baldengineer/Mega-IIe/kicad files/gd rp2040 keyboard proto pcb/kicad/README.md

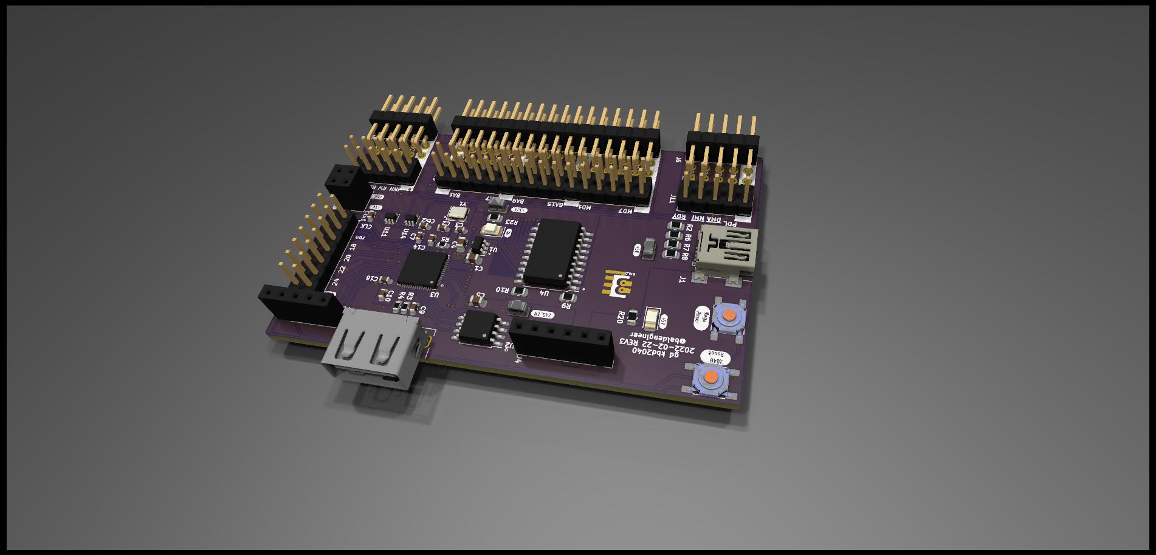
[picture p10: images/gd-rp2040-proto-pcb-rev3-render.jpg]
3d render of rp2040 board


RP2040-based board to test emulating an Apple IIe keyboard
