baldengineer/Mega-IIe/firmware/mega2_picovga/vga_mega2/bmps/facepalm_hgr.bmp

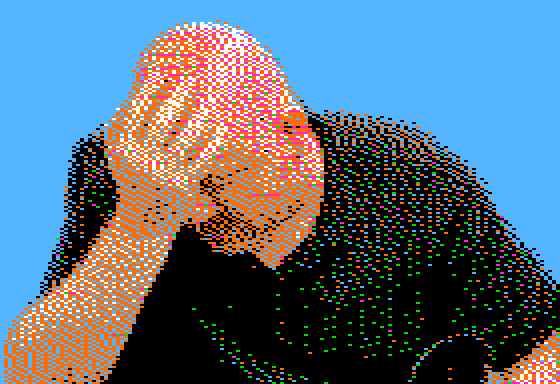
firmware/mega2_picovga/vga_mega2/bmps/facepalm_hgr.bmp
