baldengineer/Mega-IIe/images/all-rev1-boards-fusion-render.jpg

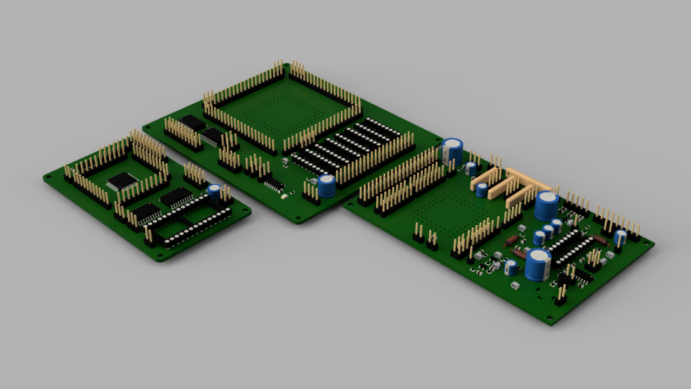
images/all-rev1-boards-fusion-render.jpg
