baldengineer/Mega-IIe/images/megaII-breakout-rev1-render.jpg

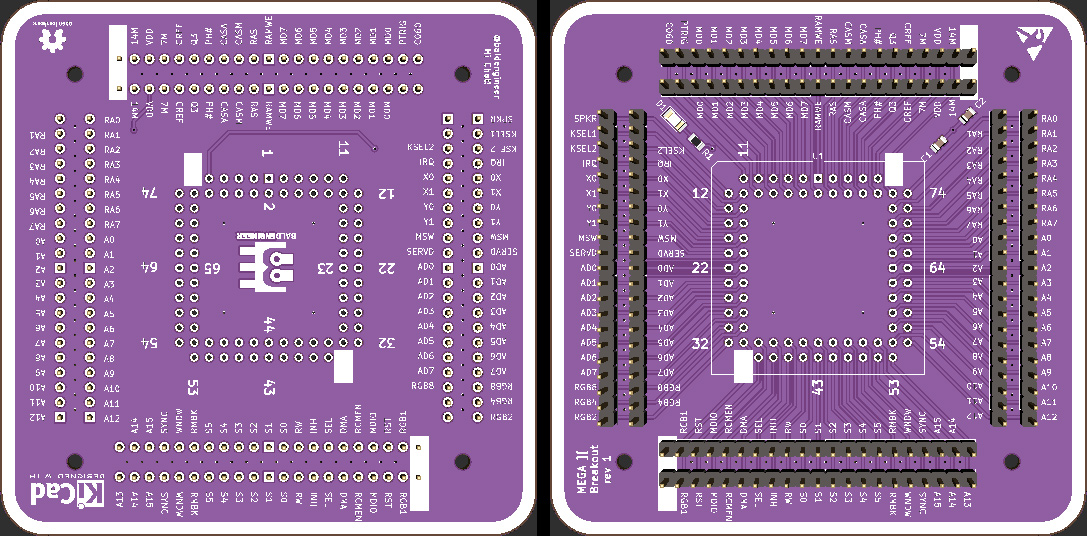
images/megaII-breakout-rev1-render.jpg
