baldengineer/Mega-IIe/kicad files/gd power supply board pcb/gd ps rev1/gd power supply board pcb-backside.jpg

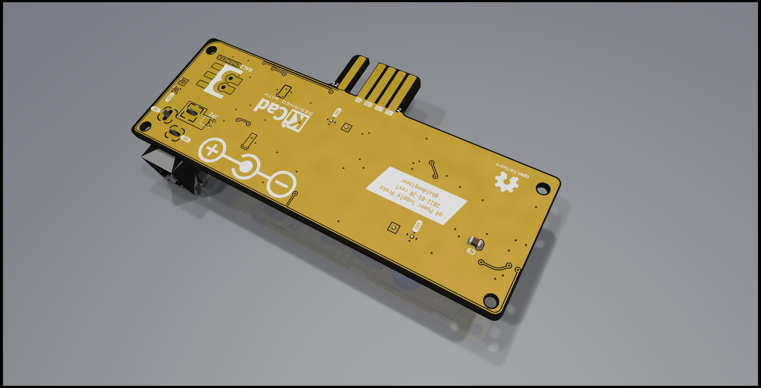
kicad files/gd power supply board pcb/gd ps rev1/gd power supply board pcb-backside.jpg
