baldengineer/Mega-IIe/kicad files/gd rp2040 keyboard proto pcb/kicad/gd rp2040 keyboard proto pcb.png

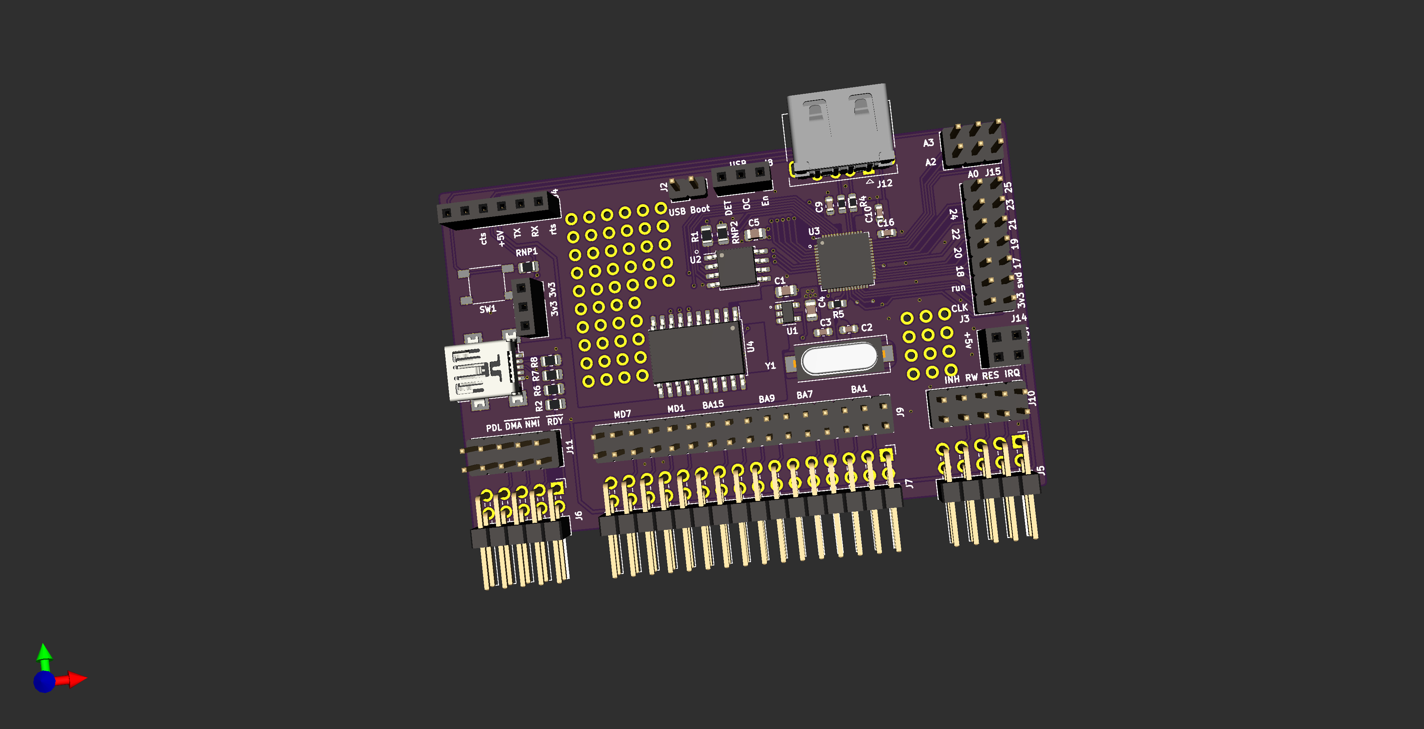
kicad files/gd rp2040 keyboard proto pcb/kicad/gd rp2040 keyboard proto pcb.png
