baldengineer/Mega-IIe/kicad files/gd slot extender/gd slot extender.jpg

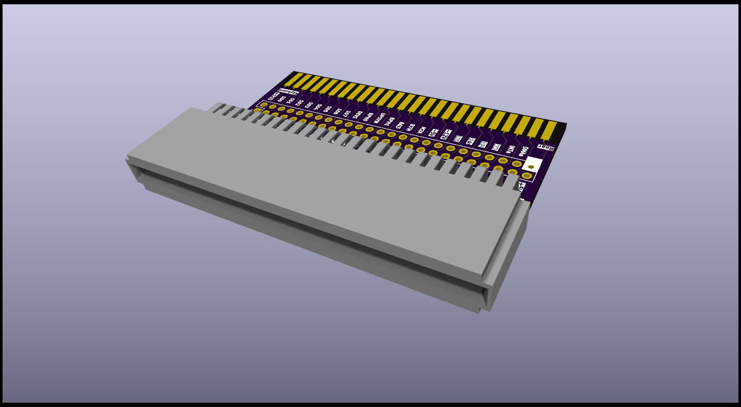
kicad files/gd slot extender/gd slot extender.jpg
