baldengineer/Mega-IIe/images/gd-rev2-proto-partial-build-up.jpg

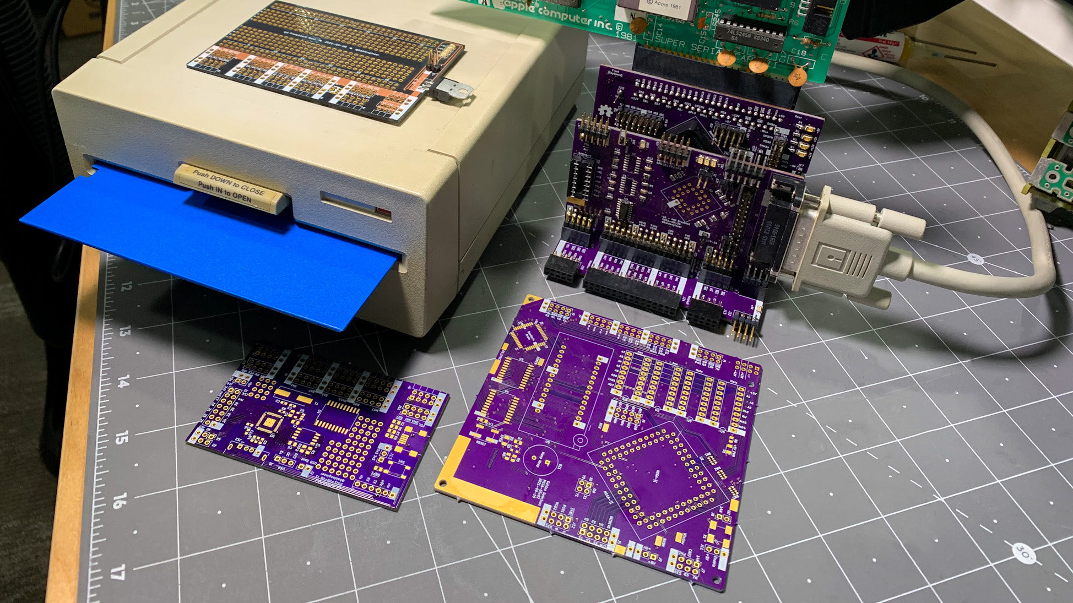
images/gd-rev2-proto-partial-build-up.jpg
