baldengineer/Mega-IIe/kicad files/gd power supply board pcb/lt-spice/input_filter_with_L.asc

C1: cap; 120µ; V=35 Irms=0 Rser=0 Lser=0 mfg="Murata" pn="GRM21BR6YA106KE43" type="X5R"
C2: cap; 10µ
C3: cap; 10n
L2: ind; 1µ; Rser=0.2
R2: res; 5
V1: voltage; AC 1
Named nets: 0
.ac dec 1000 10000 2000000
