baldengineer/Mega-IIe/kicad files/gd power supply board pcb/proto socket adapter/proto socket adapter.kicad_pcb

## KiCad design kicad files/gd power supply board pcb/proto socket adapter/proto socket adapter.kicad_pcb (2022-04-07)

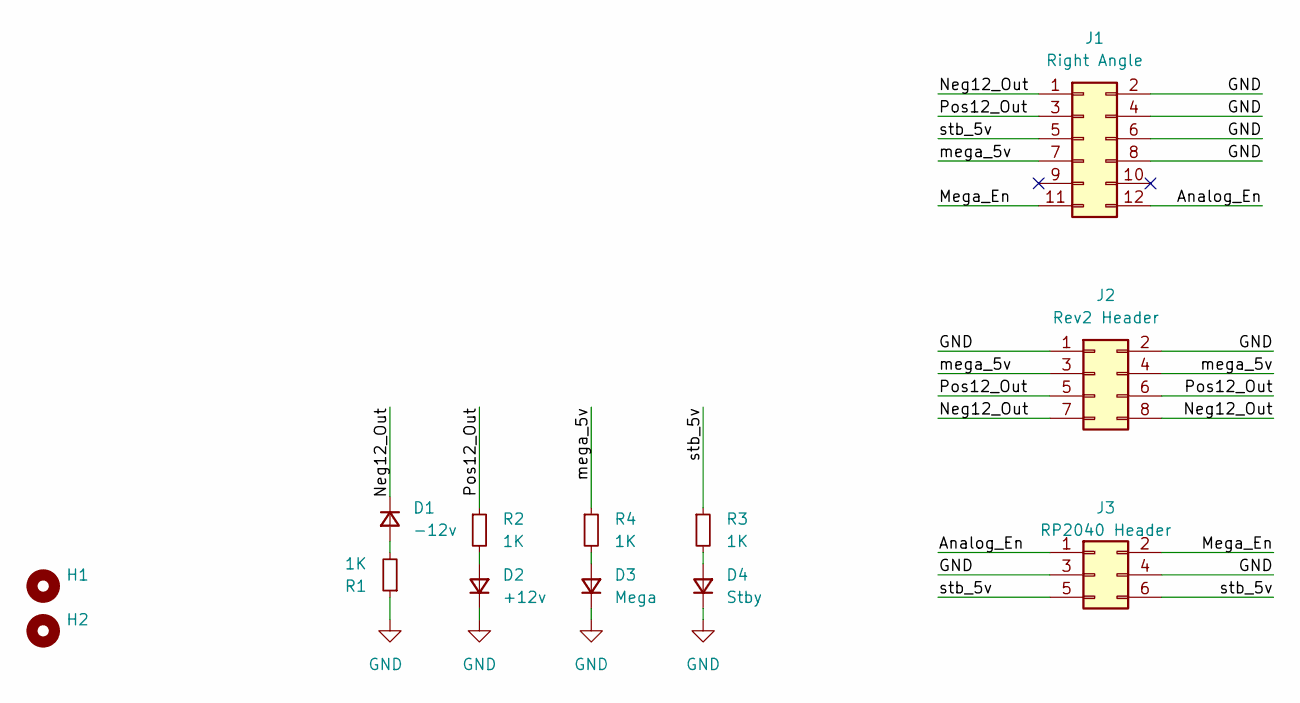
[picture p73: schematic proto socket adapter.kicad_sch]

Parts:
D1: -12v; LED_0805_2012Metric
D2: +12v; LED_0805_2012Metric
D3: Mega; LED_0805_2012Metric
D4: Stby; LED_0805_2012Metric
H1, H2: MountingHole; MountingHole_2.2mm_M2
J1: Right Angle; TE 5650118-3 Right Angle 12 Pos Socket
J2: Rev2 Header; PinSocket_2x04_P2.54mm_Vertical
J3: RP2040 Header; PinSocket_2x03_P2.54mm_Vertical
R1, R2, R3, R4: 1K; R_0805_2012Metric

Connections:
/Analog_En: J1.12, J3.1
/Mega_En: J1.11, J3.2
/Neg12_Out: D1.1 (K), J1.1, J2.7, J2.8
/Pos12_Out: J1.3, J2.5, J2.6, R2.1
/mega_5v: J1.7, J2.3, J2.4, R4.1
/stb_5v: J1.5, J3.5, J3.6, R3.1
GND: D2.1 (K), D3.1 (K), D4.1 (K), J1.2, J1.4, J1.6, J1.8, J2.1, J2.2, J3.3, J3.4, R1.1
unnamed: D1.2 (A), R1.2
unnamed: D2.2 (A), R2.2
unnamed: D3.2 (A), R4.2
unnamed: D4.2 (A), R3.2

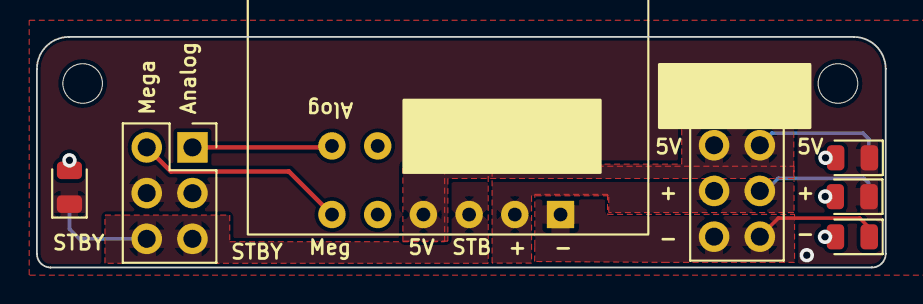
[picture p74: board proto socket adapter.kicad_pcb from above]

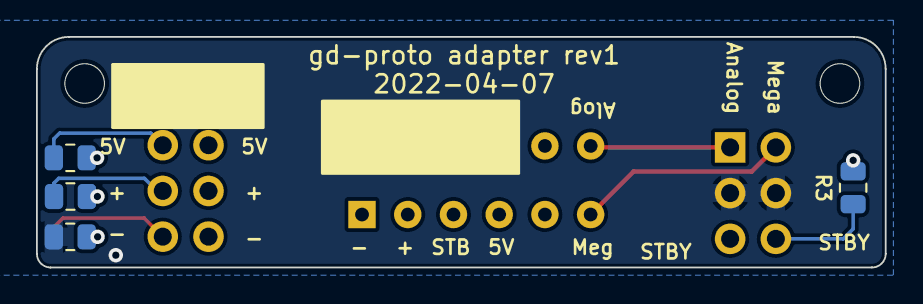
[picture p75: board proto socket adapter.kicad_pcb from below]

Board: 2 copper layers, 47.2 x 12.8 mm, 13 parts (4 on the bottom side), 11 nets.
