baldengineer/Mega-IIe/kicad files/gd rp2040 keyboard proto pcb/kicad/gd rp2040 keyboard proto pcb.kicad_pcb

## KiCad design kicad files/gd rp2040 keyboard proto pcb/kicad/gd rp2040 keyboard proto pcb.kicad_pcb (2022-02-24)

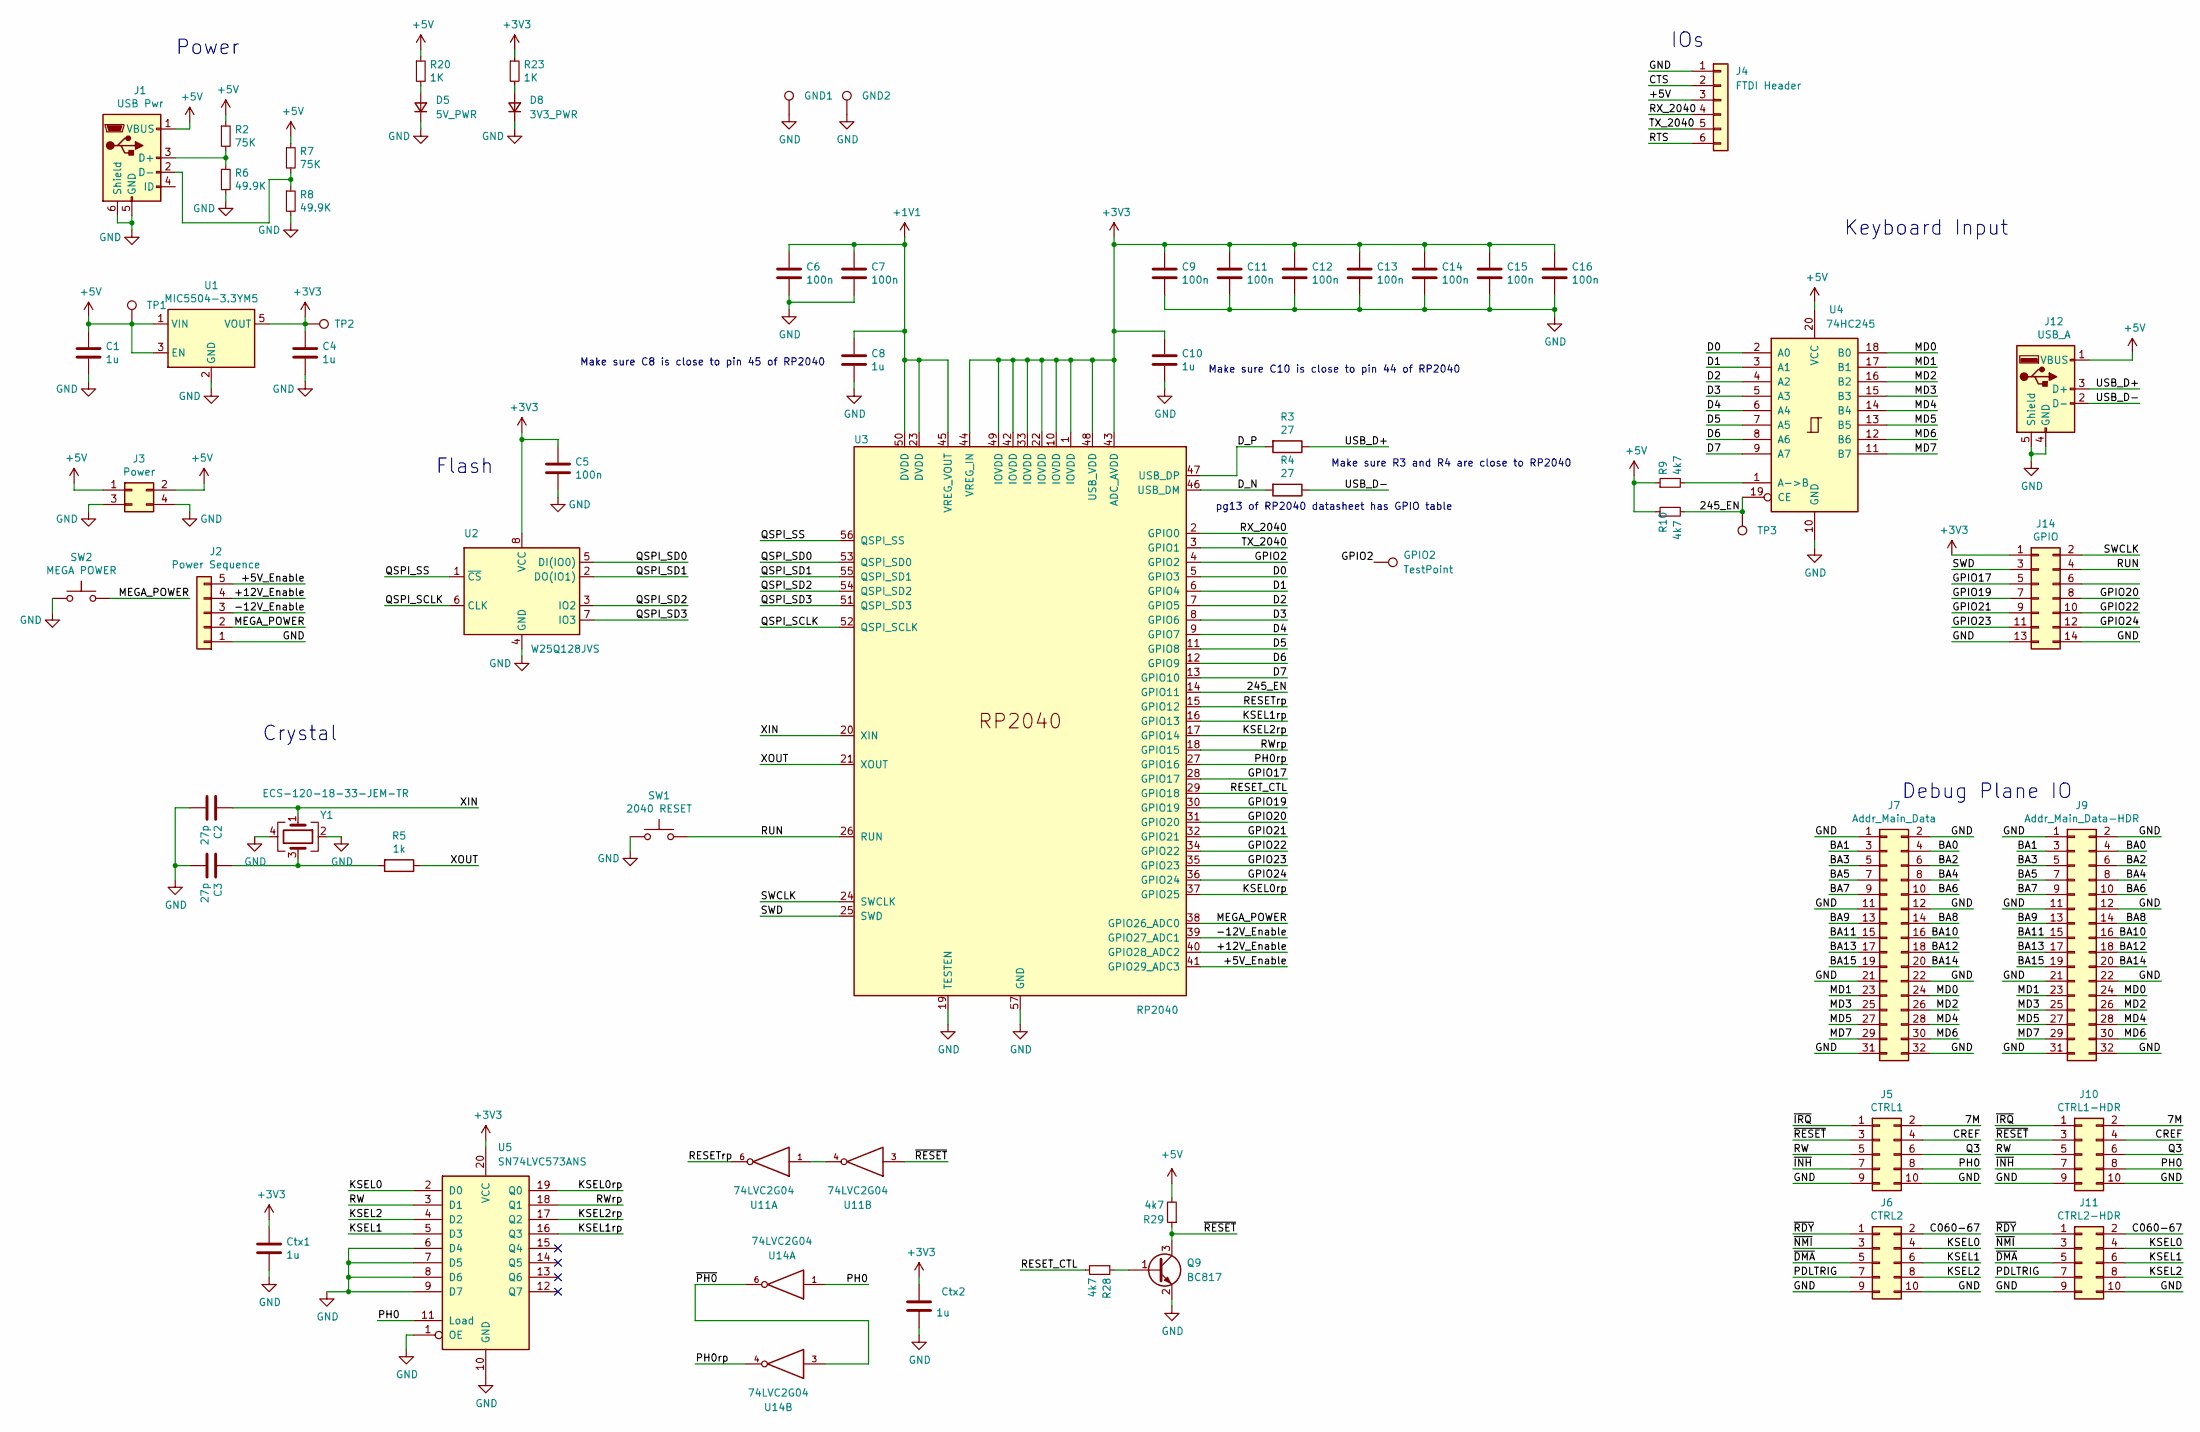
[picture p76: schematic gd rp2040 keyboard proto pcb.kicad_sch, RP2040 for Mega IIe Proto Rev2]

Parts:
C1, C4: 1u; C_0805_2012Metric
C2, C3: 27p; C_0603_1608Metric
C5: 100n; C_0805_2012Metric
C6, C7, C9, C11, C12, C13, C14, C15, C16: 100n; C_0603_1608Metric
C8, C10: 1u; C_0603_1608Metric
Ctx1, Ctx2: 1u; C_0603_1608Metric
D5: 5V_PWR; LED_1206_3216Metric
D8: 3V3_PWR; LED_1206_3216Metric
GND1, GND2: TestPoint_Harwin; Harwin-S1751-46-Test-Point
GPIO2: TestPoint; TestPoint_Pad_D1.0mm
J1: USB Pwr; USB_Mini-B_Wuerth_65100516121_Horizontal
J2: Power Sequence; PinSocket_1x05_P2.54mm_Vertical
J3: Power; PinSocket_2x02_P2.54mm_Vertical
J4: FTDI Header; PinSocket_1x06_P2.54mm_Vertical
J5: CTRL1; PinHeader_2x05_P2.54mm_Horizontal
J6: CTRL2; PinHeader_2x05_P2.54mm_Horizontal
J7: Addr_Main_Data; PinHeader_2x16_P2.54mm_Horizontal
J9: Addr_Main_Data-HDR; PinHeader_2x16_P2.54mm_Vertical
J10: CTRL1-HDR; PinHeader_2x05_P2.54mm_Vertical
J11: CTRL2-HDR; PinHeader_2x05_P2.54mm_Vertical
J12: USB_A; USB_A_GCT_USB1125; MPN USB1125-GF-B
J14: GPIO; PinHeader_2x07_P2.54mm_Vertical
Q9: BC817; SOT-23
R2, R7: 75K; R_0805_2012Metric
R3, R4: 27; R_0603_1608Metric
R5: 1k; R_0603_1608Metric
R6, R8: 49.9K; R_0805_2012Metric
R9, R10, R28, R29: 4k7; R_0805_2012Metric
R20, R23: 1K; R_0805_2012Metric
SW1: 2040 RESET; SW_Push_CK_PTS525_SM15
SW2: MEGA POWER; SW_Push_CK_PTS525_SM15
TP1, TP2, TP3: TestPoint_Harwin; Harwin-S1751-46-Test-Point
U1: MIC5504-3.3YM5; SOT-23-5
U2: W25Q128JVS; SOIC-8_5.23x5.23mm_P1.27mm
U3: RP2040; RP2040-QFN-56
U4: 74HC245; SOIC-20W_7.5x12.8mm_P1.27mm
U5: SN74LVC573ANS; SO-20_5.3x12.6mm_P1.27mm
U11, U14: 74LVC2G04; SOT-363_SC-70-6
Y1: ECS-120-18-33-JEM-TR; Crystal_SMD_3225-4Pin_3.2x2.5mm

Connections:
+1V1: C6.1, C7.1, C8.1, U3.23 (DVDD), U3.45 (VREG_VOUT), U3.50 (DVDD)
+3V3: C4.1, C5.1, C9.1, C10.1, C11.1, C12.1, C13.1, C14.1, C15.1, C16.1, Ctx1.1, Ctx2.1, J14.1, R23.1, TP2.1, U1.5 (VOUT), U2.8 (VCC), U3.1 (IOVDD), U3.10 (IOVDD), U3.22 (IOVDD), U3.33 (IOVDD), U3.42 (IOVDD), U3.43 (ADC_AVDD), U3.44 (VREG_IN), U3.48 (USB_VDD), U3.49 (IOVDD), U5.20 (VCC), U11.5 (+3V3), U14.5 (+3V3)
+5V: C1.1, J1.1 (VBUS), J3.1, J3.2, J4.3, J12.1 (VBUS), R2.1, R7.1, R9.1, R10.1, R20.1, R29.2, TP1.1, U1.1 (VIN), U1.3 (EN), U4.20 (VCC)
/7M: J5.2, J10.2
/245_EN: R10.2, TP3.1, U3.14 (GPIO11), U4.19 (CE)
/+5V_Enable: J2.5, U3.41 (GPIO29_ADC3)
/+12V_Enable: J2.4, U3.40 (GPIO28_ADC2)
/-12V_Enable: J2.3, U3.39 (GPIO27_ADC1)
/BA0: J7.4, J9.4
/BA1: J7.3, J9.3
/BA2: J7.6, J9.6
/BA3: J7.5, J9.5
/BA4: J7.8, J9.8
/BA5: J7.7, J9.7
/BA6: J7.10, J9.10
/BA7: J7.9, J9.9
/BA8: J7.14, J9.14
/BA9: J7.13, J9.13
/BA10: J7.16, J9.16
/BA11: J7.15, J9.15
/BA12: J7.18, J9.18
/BA13: J7.17, J9.17
/BA14: J7.20, J9.20
/BA15: J7.19, J9.19
/C060-67: J6.2, J11.2
/CREF: J5.4, J10.4
/CTS: J4.2
/D0: U3.5 (GPIO3), U4.2 (A0)
/D1: U3.6 (GPIO4), U4.3 (A1)
/D2: U3.7 (GPIO5), U4.4 (A2)
/D3: U3.8 (GPIO6), U4.5 (A3)
/D4: U3.9 (GPIO7), U4.6 (A4)
/D5: U3.11 (GPIO8), U4.7 (A5)
/D6: U3.12 (GPIO9), U4.8 (A6)
/D7: U3.13 (GPIO10), U4.9 (A7)
/D_N: R4.2, U3.46 (USB_DM)
/D_P: R3.2, U3.47 (USB_DP)
/GPIO2: GPIO2.1, U3.4 (GPIO2)
/GPIO17: J14.5, U3.28 (GPIO17)
/GPIO19: J14.7, U3.30 (GPIO19)
/GPIO20: J14.8, U3.31 (GPIO20)
/GPIO21: J14.9, U3.32 (GPIO21)
/GPIO22: J14.10, U3.34 (GPIO22)
/GPIO23: J14.11, U3.35 (GPIO23)
/GPIO24: J14.12, U3.36 (GPIO24)
/KSEL0: J6.4, J11.4, U5.2 (D0)
/KSEL0rp: U3.37 (GPIO25), U5.19 (Q0)
/KSEL1: J6.6, J11.6, U5.5 (D3)
/KSEL1rp: U3.16 (GPIO13), U5.16 (Q3)
/KSEL2: J6.8, J11.8, U5.4 (D2)
/KSEL2rp: U3.17 (GPIO14), U5.17 (Q2)
/MD0: J7.24, J9.24, U4.18 (B0)
/MD1: J7.23, J9.23, U4.17 (B1)
/MD2: J7.26, J9.26, U4.16 (B2)
/MD3: J7.25, J9.25, U4.15 (B3)
/MD4: J7.28, J9.28, U4.14 (B4)
/MD5: J7.27, J9.27, U4.13 (B5)
/MD6: J7.30, J9.30, U4.12 (B6)
/MD7: J7.29, J9.29, U4.11 (B7)
/MEGA_POWER: J2.2, SW2.2, U3.38 (GPIO26_ADC0)
/PDLTRIG: J6.7, J11.7
/PH0: J5.8, J10.8, U5.11 (Load), U14.1
/PH0rp: U3.27 (GPIO16), U14.4
/Q3: J5.6, J10.6
/QSPI_SCLK: U2.6 (CLK), U3.52 (QSPI_SCLK)
/QSPI_SD0: U2.5 (DI(IO0)), U3.53 (QSPI_SD0)
/QSPI_SD1: U2.2 (DO(IO1)), U3.55 (QSPI_SD1)
/QSPI_SD2: U2.3 (IO2), U3.54 (QSPI_SD2)
/QSPI_SD3: U2.7 (IO3), U3.51 (QSPI_SD3)
/QSPI_SS: U2.1 (~CS), U3.56 (QSPI_SS)
/RESET_CTL: R28.2, U3.29 (GPIO18)
/RESETrp: U3.15 (GPIO12), U11.6
/RTS: J4.6
/RUN: J14.4, SW1.2, U3.26 (RUN)
/RW: J5.5, J10.5, U5.3 (D1)
/RWrp: U3.18 (GPIO15), U5.18 (Q1)
/RX_2040: J4.4, U3.2 (GPIO0)
/SWCLK: J14.2, U3.24 (SWCLK)
/SWD: J14.3, U3.25 (SWD)
/TX_2040: J4.5, U3.3 (GPIO1)
/USB_D+: J12.3 (D+), R3.1
/USB_D-: J12.2 (D-), R4.1
/XIN: C2.1, U3.20 (XIN), Y1.1
/XOUT: R5.1, U3.21 (XOUT)
/~DMA: J6.5, J11.5
/~INH: J5.7, J10.7
/~IRQ: J5.1, J10.1
/~NMI: J6.3, J11.3
/~PH0: U14.3, U14.6
/~RDY: J6.1, J11.1
/~RESET: J5.3, J10.3, Q9.3 (C), R29.1, U11.3
GND: C1.2, C2.2, C3.2, C4.2, C5.2, C6.2, C7.2, C8.2, C9.2, C10.2, C11.2, C12.2, C13.2, C14.2, C15.2, C16.2, Ctx1.2, Ctx2.2, D5.1 (K), D8.1 (K), GND1.1, GND2.1, J1.5 (GND), J1.6 (Shield), J2.1, J3.3, J3.4, J4.1, J5.9, J5.10, J6.9, J6.10, J7.1, J7.2, J7.11, J7.12, J7.21, J7.22, J7.31, J7.32, J9.1, J9.2, J9.11, J9.12, J9.21, J9.22, J9.31, J9.32, J10.9, J10.10, J11.9, J11.10, J12.4 (GND), J12.5 (Shield), J14.13, J14.14, Q9.2 (E), R6.2, R8.2, SW1.1, SW2.1, U1.2 (GND), U2.4 (GND), U3.19 (TESTEN), U3.57 (GND), U4.10 (GND), U5.1 (OE), U5.6 (D4), U5.7 (D5), U5.8 (D6), U5.9 (D7), U5.10 (GND), U11.2 (GND), U14.2 (GND), Y1.2, Y1.4
unnamed: C3.1, R5.2, Y1.3
unnamed: D5.2 (A), R20.2
unnamed: D8.2 (A), R23.2
unnamed: J1.2 (D-), R7.2, R8.1
unnamed: J1.3 (D+), R2.2, R6.1
unnamed: Q9.1 (B), R28.1
unnamed: R9.2, U4.1 (A->B)
unnamed: U11.1, U11.4

Notes on the sheet:
Make sure C8 is close to pin 45 of RP2040
Crystal
Flash
IOs
pg13 of RP2040 datasheet has GPIO table
Keyboard Input
Make sure R3 and R4 are close to RP2040
Power
Make sure C10 is close to pin 44 of RP2040
Debug Plane IO

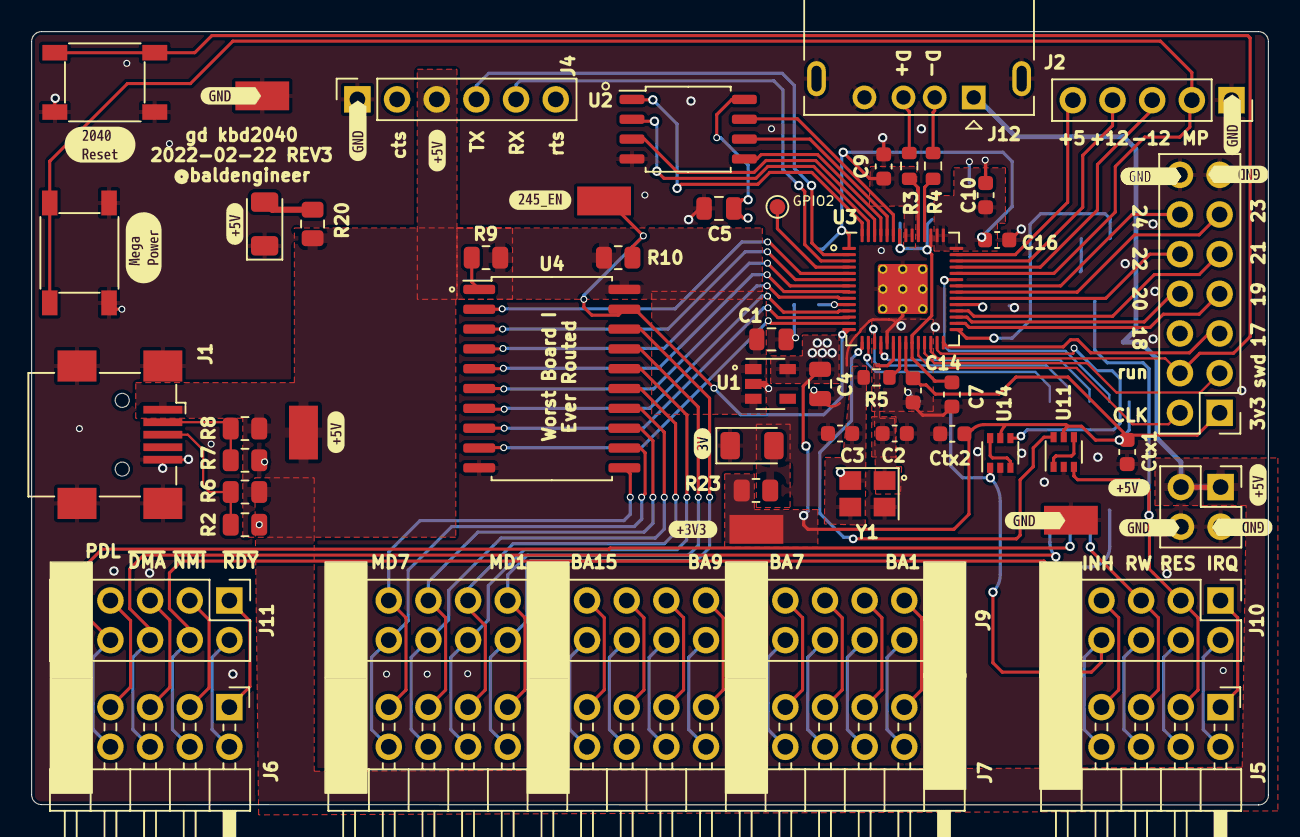
[picture p77: board gd rp2040 keyboard proto pcb.kicad_pcb from above]

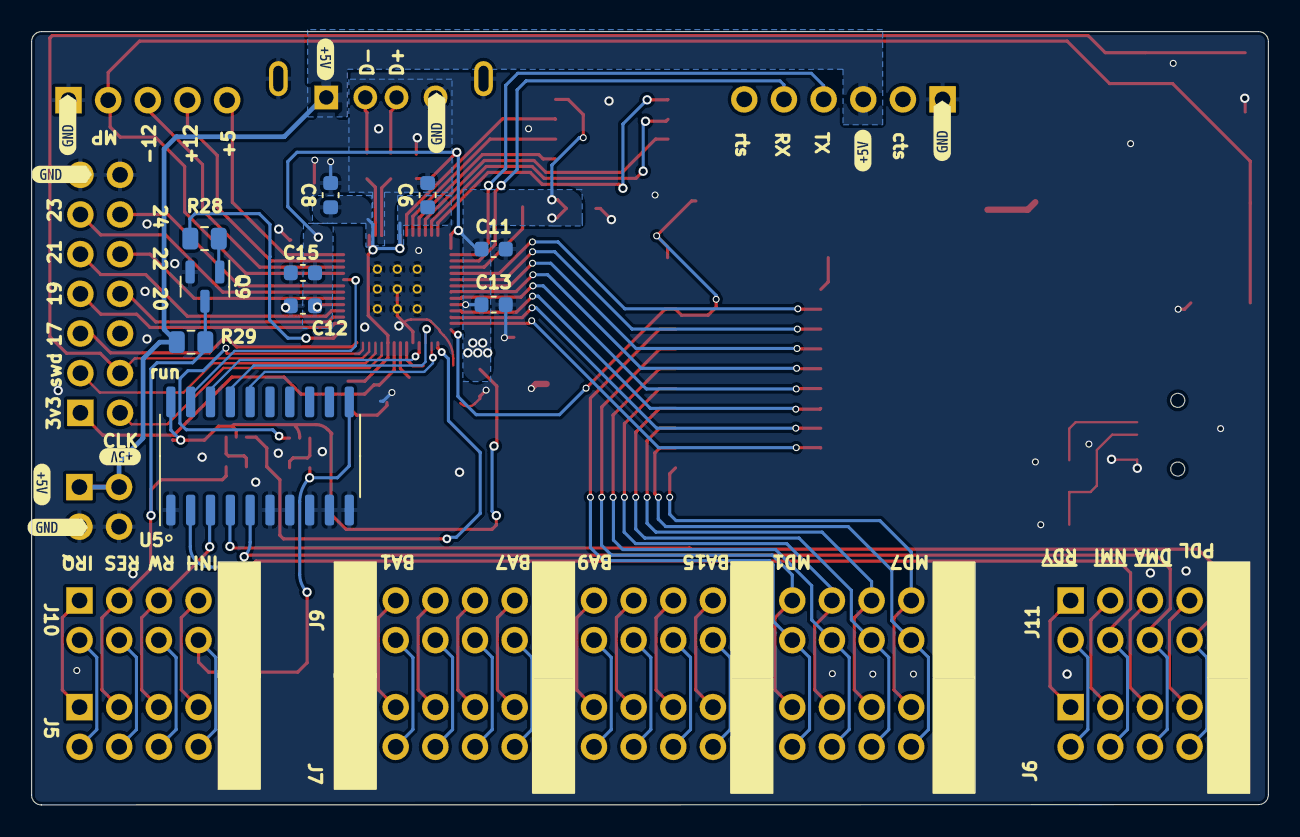
[picture p78: board gd rp2040 keyboard proto pcb.kicad_pcb from below]

Board: 2 copper layers, 79.2 x 49.5 mm, 90 parts (19 on the bottom side), 98 nets.

Other parts of the board:
kibuzzard-6215C1CA: G***; kibuzzard-6215C1CA
kibuzzard-62158D6B: G***; kibuzzard-62158D6B
kibuzzard-62158D92, kibuzzard-62158D92#2, kibuzzard-62158D92#3, kibuzzard-62158D92#4, kibuzzard-62158D92#5, kibuzzard-62158D92#6, kibuzzard-62158D92#7, kibuzzard-62158D92#8, kibuzzard-62158D92#9: G***; kibuzzard-62158D92
kibuzzard-62158DE7: G***; kibuzzard-62158DE7
kibuzzard-62158E3B: G***; kibuzzard-62158E3B
kibuzzard-62158E96, kibuzzard-62158E96#2, kibuzzard-62158E96#3, kibuzzard-62158E96#4, kibuzzard-62158E96#5, kibuzzard-62158E96#6, kibuzzard-62158E96#7, kibuzzard-62158E96#8, kibuzzard-62158E96#9, kibuzzard-62158E96#10, kibuzzard-62158E96#11, kibuzzard-62158E96#12, kibuzzard-62158E96#13, kibuzzard-62158E96#14: G***; kibuzzard-62158E96
kibuzzard-621593E3: G***; kibuzzard-621593E3
