baldengineer/Mega-IIe/kicad files/gd vga pico proto pcb/gd vga pico proto pcb.kicad_pcb

## KiCad design kicad files/gd vga pico proto pcb/gd vga pico proto pcb.kicad_pcb (2022-02-22)

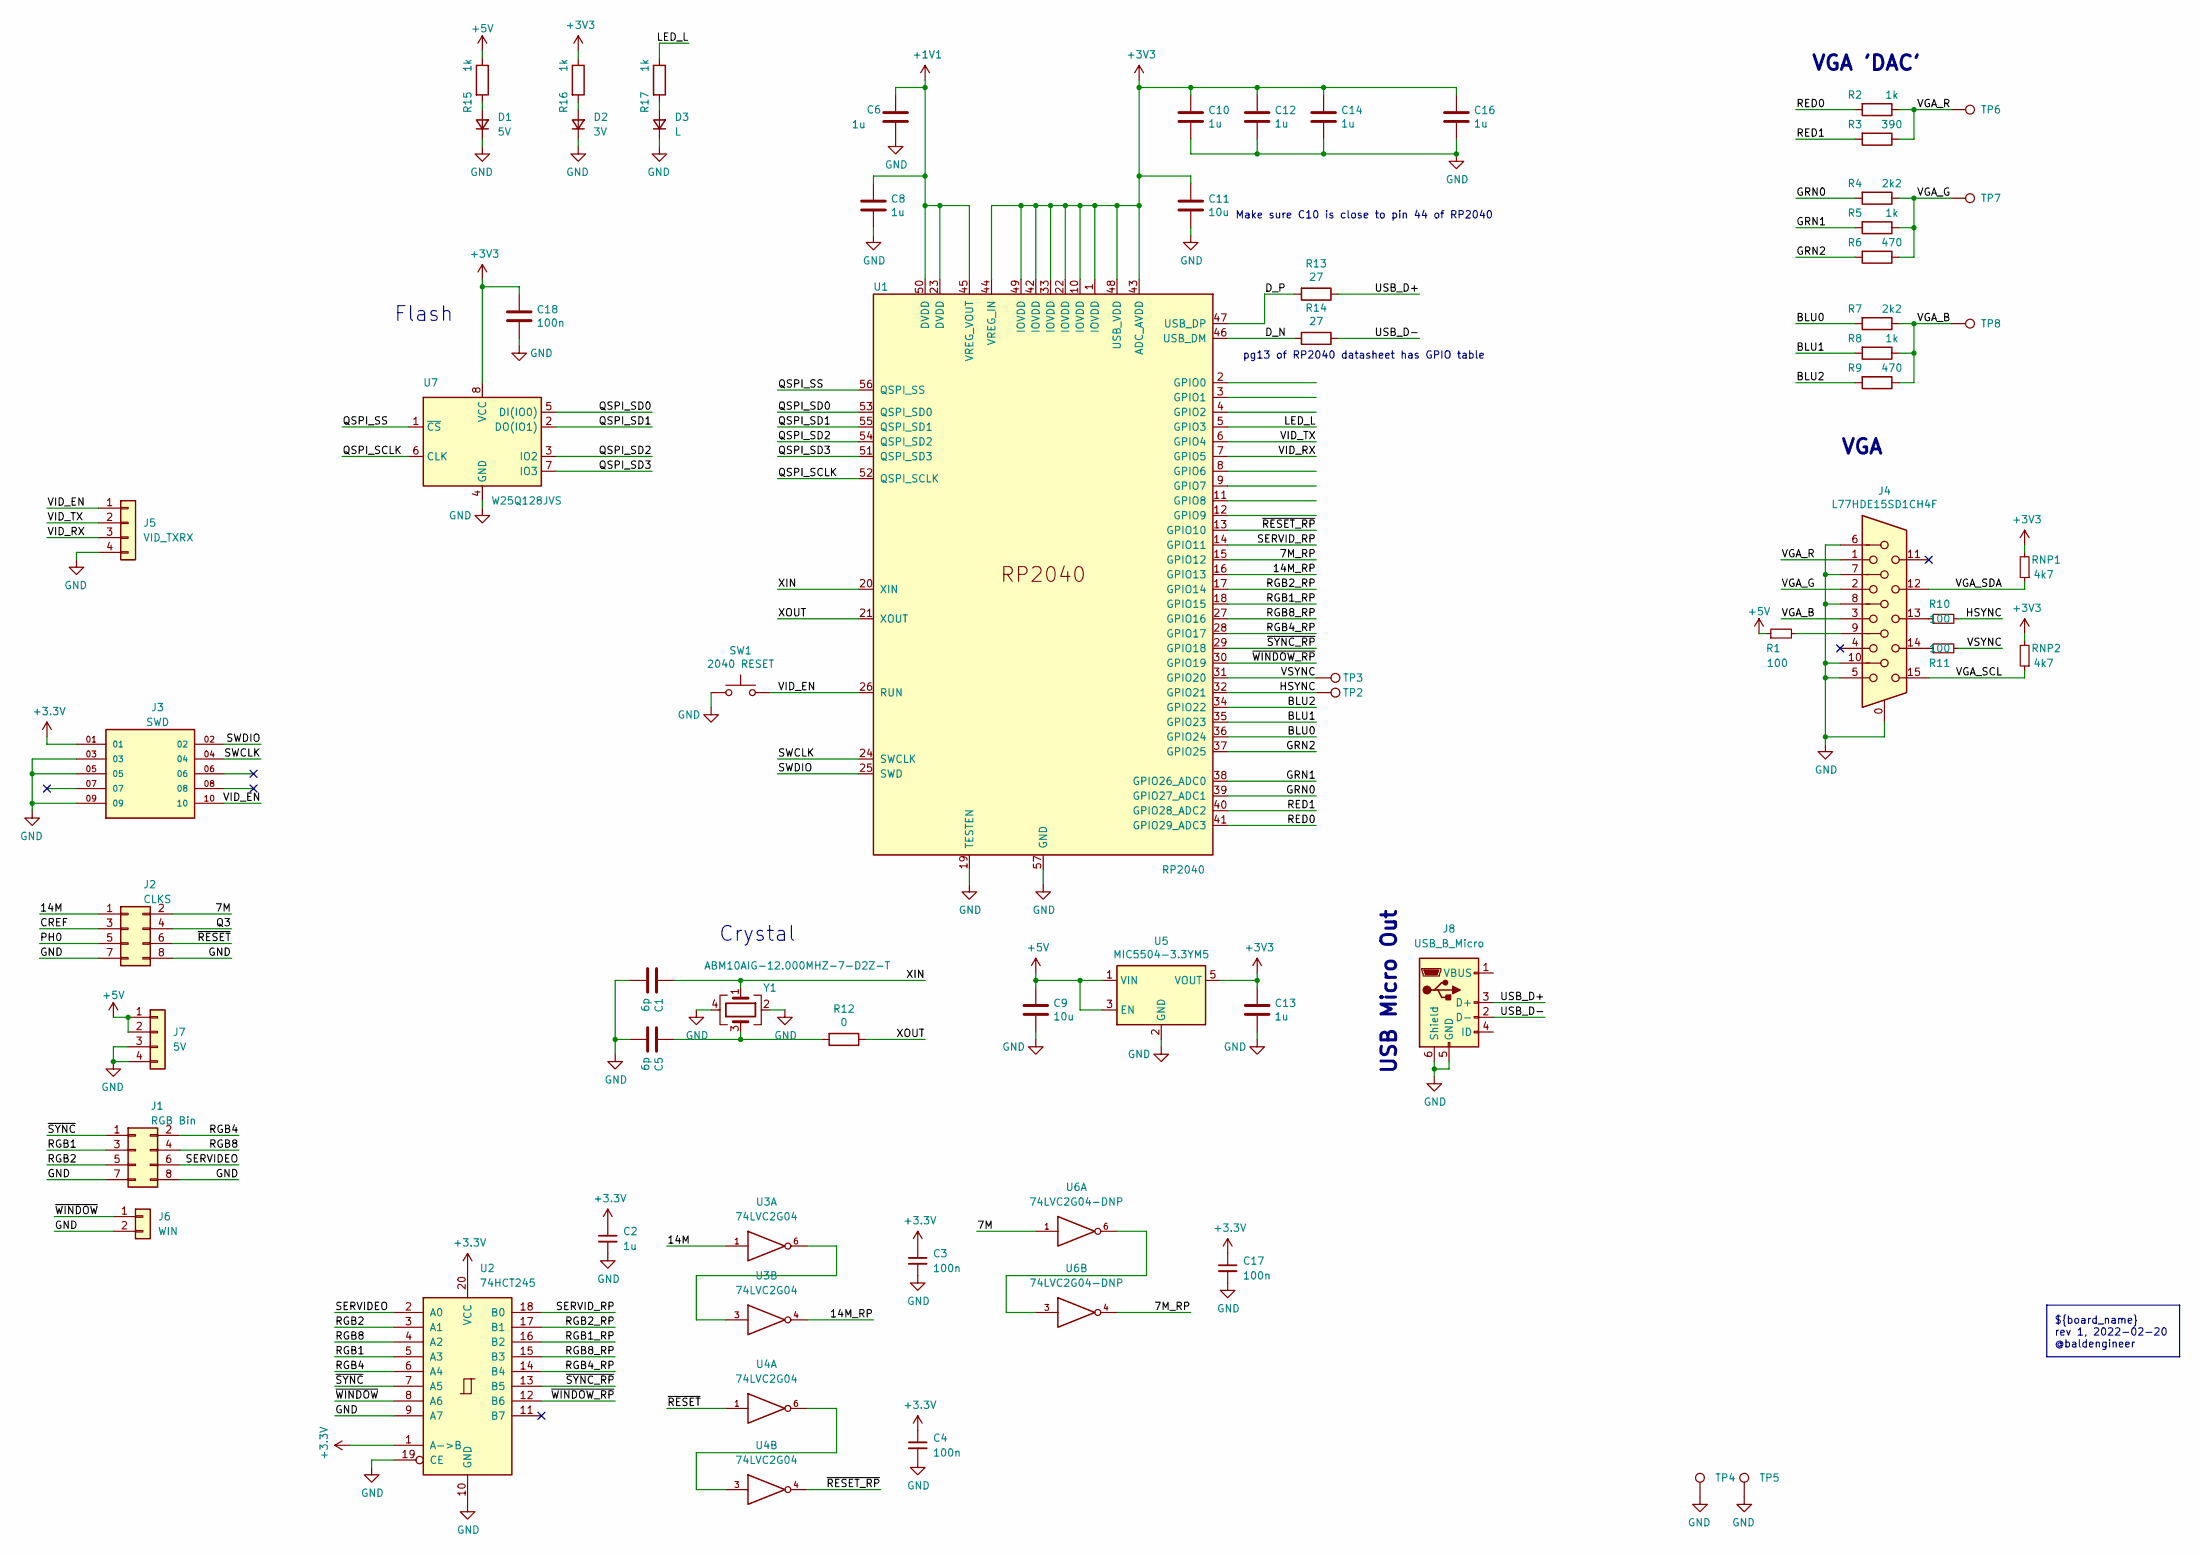
[picture p79: schematic gd vga pico proto pcb.kicad_sch, VGA Pico Proto]

Parts:
C1, C5: 6p; C_0402_1005Metric
C2, C6, C8, C10, C12, C13, C14, C16: 1u; C_0603_1608Metric
C3, C4, C17: 100n; C_0603_1608Metric
C9, C11: 10u; C_0805_2012Metric
C18: 100n; C_0805_2012Metric
D1: 5V; LED_1206_3216Metric
D2: 3V; LED_1206_3216Metric
D3: L; LED_1206_3216Metric
J1: RGB Bin; PinSocket_2x04_P2.54mm_Vertical
J2: CLKS; PinSocket_2x04_P2.54mm_Vertical
J3: SWD; SAMTEC_FTSH-105-XX-X-DV; PARTREV H
J4: L77HDE15SD1CH4F; AMPHENOL_L77HDE15SD1CH4F
J5: VID_TXRX; PinHeader_1x04_P2.54mm_Vertical
J6: WIN; PinHeader_1x02_P2.54mm_Vertical
J7: 5V; PinSocket_1x04_P2.54mm_Vertical
J8: USB_B_Micro; USB_Micro-B_GCT_USB3076-30-A
R1, R10, R11: 100; R_0603_1608Metric
R2, R5, R8, R15, R16, R17: 1k; R_0603_1608Metric
R3: 390; R_0603_1608Metric
R4, R7: 2k2; R_0603_1608Metric
R6, R9: 470; R_0603_1608Metric
R12: 0; R_0603_1608Metric
R13, R14: 27; R_0603_1608Metric
RNP1, RNP2: 4k7; R_0603_1608Metric
SW1: 2040 RESET; SW_Push_CK_PTS525_SM15
TP2, TP3, TP4, TP5, TP6, TP7, TP8: TestPoint_Harwin; Harwin-S1751-46-Test-Point
U1: RP2040; RP2040-QFN-56
U2: 74HCT245; SO-20_5.3x12.6mm_P1.27mm
U3, U4: 74LVC2G04; SOT-23-6
U5: MIC5504-3.3YM5; SOT-23-5
U6: 74LVC2G04-DNP; SOT-23-6
U7: W25Q128JVS; SOIC-8_5.23x5.23mm_P1.27mm
Y1: ABM10AIG-12.000MHZ-7-D2Z-T; Crystal_SMD_2520-4Pin_2.5x2.0mm

Connections:
+1V1: C6.1, C8.1, U1.23 (DVDD), U1.45 (VREG_VOUT), U1.50 (DVDD)
+5V: C9.1, J7.1, J7.2, R1.1, R15.1, U5.1 (VIN), U5.3 (EN)
/7M: J2.2, U6.1
/7M_RP: U1.15 (GPIO12), U6.4
/14M: J2.1, U3.1
/14M_RP: U1.16 (GPIO13), U3.4
/BLU0: R7.2, U1.36 (GPIO24)
/BLU1: R8.2, U1.35 (GPIO23)
/BLU2: R9.2, U1.34 (GPIO22)
/CREF: J2.3
/D_N: R14.2, U1.46 (USB_DM)
/D_P: R13.2, U1.47 (USB_DP)
/GRN0: R4.2, U1.39 (GPIO27_ADC1)
/GRN1: R5.2, U1.38 (GPIO26_ADC0)
/GRN2: R6.2, U1.37 (GPIO25)
/HSYNC: R10.2, TP2.1, U1.32 (GPIO21)
/LED_L: R17.1, U1.5 (GPIO3)
/PH0: J2.5
/Q3: J2.4
/QSPI_SCLK: U1.52 (QSPI_SCLK), U7.6 (CLK)
/QSPI_SD0: U1.53 (QSPI_SD0), U7.5 (DI(IO0))
/QSPI_SD1: U1.55 (QSPI_SD1), U7.2 (DO(IO1))
/QSPI_SD2: U1.54 (QSPI_SD2), U7.3 (IO2)
/QSPI_SD3: U1.51 (QSPI_SD3), U7.7 (IO3)
/QSPI_SS: U1.56 (QSPI_SS), U7.1 (~CS)
/RED0: R2.2, U1.41 (GPIO29_ADC3)
/RED1: R3.2, U1.40 (GPIO28_ADC2)
/RGB1: J1.3, U2.5 (A3)
/RGB1_RP: U1.18 (GPIO15), U2.16 (B2)
/RGB2: J1.5, U2.3 (A1)
/RGB2_RP: U1.17 (GPIO14), U2.17 (B1)
/RGB4: J1.2, U2.6 (A4)
/RGB4_RP: U1.28 (GPIO17), U2.14 (B4)
/RGB8: J1.4, U2.4 (A2)
/RGB8_RP: U1.27 (GPIO16), U2.15 (B3)
/SERVIDEO: J1.6, U2.2 (A0)
/SERVID_RP: U1.14 (GPIO11), U2.18 (B0)
/SWCLK: J3.04, U1.24 (SWCLK)
/SWDIO: J3.02, U1.25 (SWD)
/USB_D+: J8.3 (D+), R13.1
/USB_D-: J8.2 (D-), R14.1
/VGA_B: J4.3, R7.1, R8.1, R9.1, TP8.1
/VGA_G: J4.2, R4.1, R5.1, R6.1, TP7.1
/VGA_R: J4.1, R2.1, R3.1, TP6.1
/VGA_SCL: J4.15, RNP2.1
/VGA_SDA: J4.12, RNP1.1
/VID_EN: J3.10, J5.1, SW1.2, U1.26 (RUN)
/VID_RX: J5.3, U1.7 (GPIO5)
/VID_TX: J5.2, U1.6 (GPIO4)
/VSYNC: R11.2, TP3.1, U1.31 (GPIO20)
/XIN: C1.1, U1.20 (XIN), Y1.1
/XOUT: R12.1, U1.21 (XOUT)
/~RESET_RP: U1.13 (GPIO10), U4.4
/~RESET: J2.6, U4.1
/~SYNC_RP: U1.29 (GPIO18), U2.13 (B5)
/~SYNC: J1.1, U2.7 (A5)
/~WINDOW_RP: U1.30 (GPIO19), U2.12 (B6)
/~WINDOW: J6.1, U2.8 (A6)
GND: C1.2, C2.2, C3.2, C4.2, C5.2, C6.2, C8.2, C9.2, C10.2, C11.2, C12.2, C13.2, C14.2, C16.2, C17.2, C18.2, D1.1 (K), D2.1 (K), D3.1 (K), J1.7, J1.8, J2.7, J2.8, J3.03, J3.05, J3.09, J4.0, J4.5, J4.6, J4.7, J4.8, J4.10, J5.4, J6.2, J7.3, J7.4, J8.5 (GND), J8.6 (Shield), SW1.1, TP4.1, TP5.1, U1.19 (TESTEN), U1.57 (GND), U2.9 (A7), U2.10 (GND), U2.19 (CE), U3.2 (GND), U4.2 (GND), U5.2 (GND), U6.2 (GND), U7.4 (GND), Y1.2, Y1.4
unnamed: C5.1, R12.2, Y1.3
unnamed: D1.2 (A), R15.2
unnamed: D2.2 (A), R16.2
unnamed: D3.2 (A), R17.2
unnamed: J4.9, R1.2
unnamed: J4.13, R10.1
unnamed: J4.14, R11.1
unnamed: U3.3, U3.6
unnamed: U4.3, U4.6
unnamed: U6.3, U6.6

Notes on the sheet:
Make sure C10 is close to pin 44 of RP2040
Crystal
USB Micro Out
Flash
VGA 'DAC'
${board_name} rev ${REVISION}, ${ISSUE_DATE} @baldengineer
VGA
pg13 of RP2040 datasheet has GPIO table

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
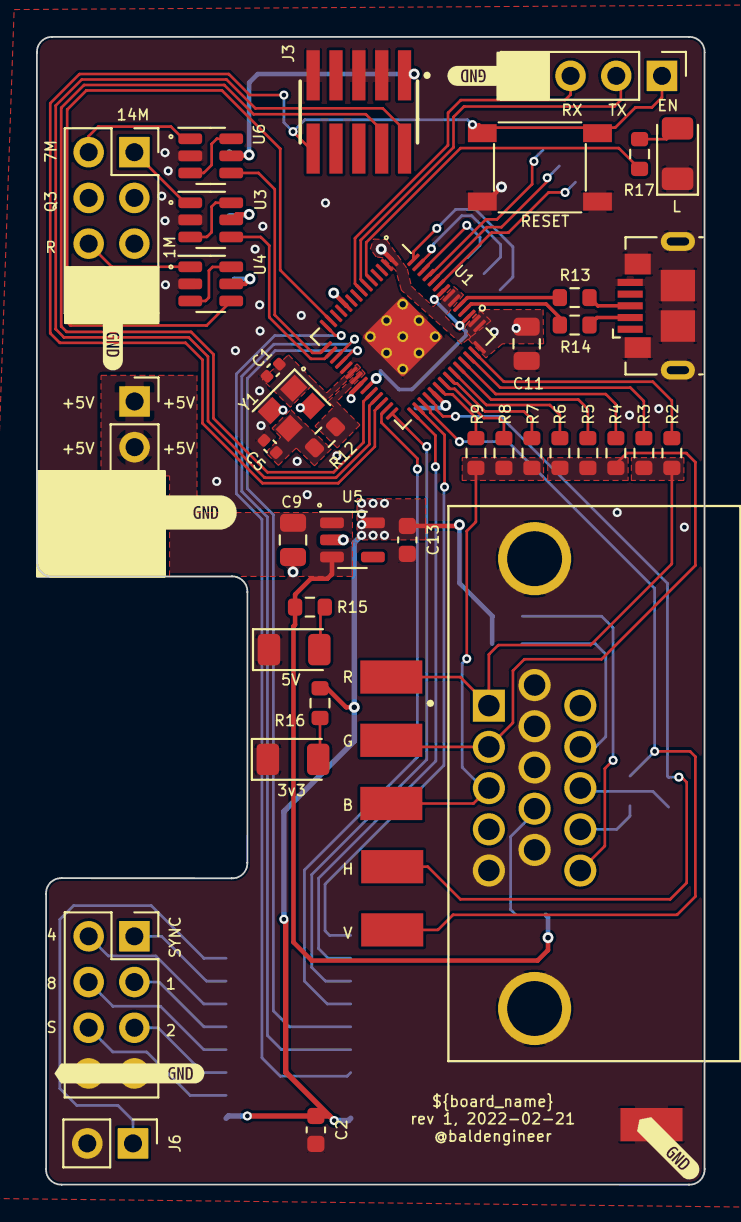
[picture p80: board gd vga pico proto pcb.kicad_pcb from above]

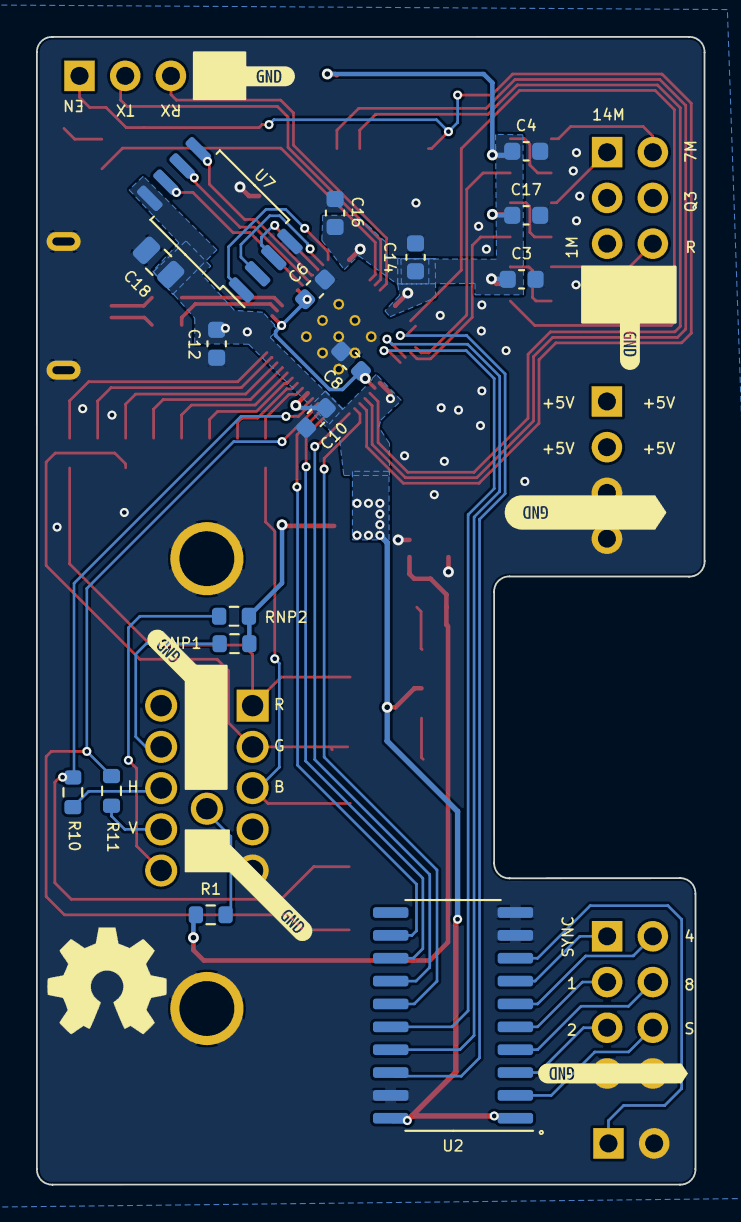
[picture p81: board gd vga pico proto pcb.kicad_pcb from below]

Board: 2 copper layers, 37.1 x 63.8 mm, 73 parts (23 on the bottom side), 67 nets.

Other parts of the board:
kibuzzard-621468FD, kibuzzard-621468FD#2: G***; kibuzzard-621468FD
kibuzzard-621469E6, kibuzzard-621469E6#2, kibuzzard-621469E6#3, kibuzzard-621469E6#4, kibuzzard-621469E6#5, kibuzzard-621469E6#6: G***; kibuzzard-621469E6
kibuzzard-62146889, kibuzzard-62146889#2, kibuzzard-62146889#3: G***; kibuzzard-62146889
