baldengineer/Mega-IIe/kicad files/gd backplane proto pcb/gd blackplane proto pcb.kicad_pcb

## KiCad design kicad files/gd backplane proto pcb/gd blackplane proto pcb.kicad_pcb (2022-02-10)

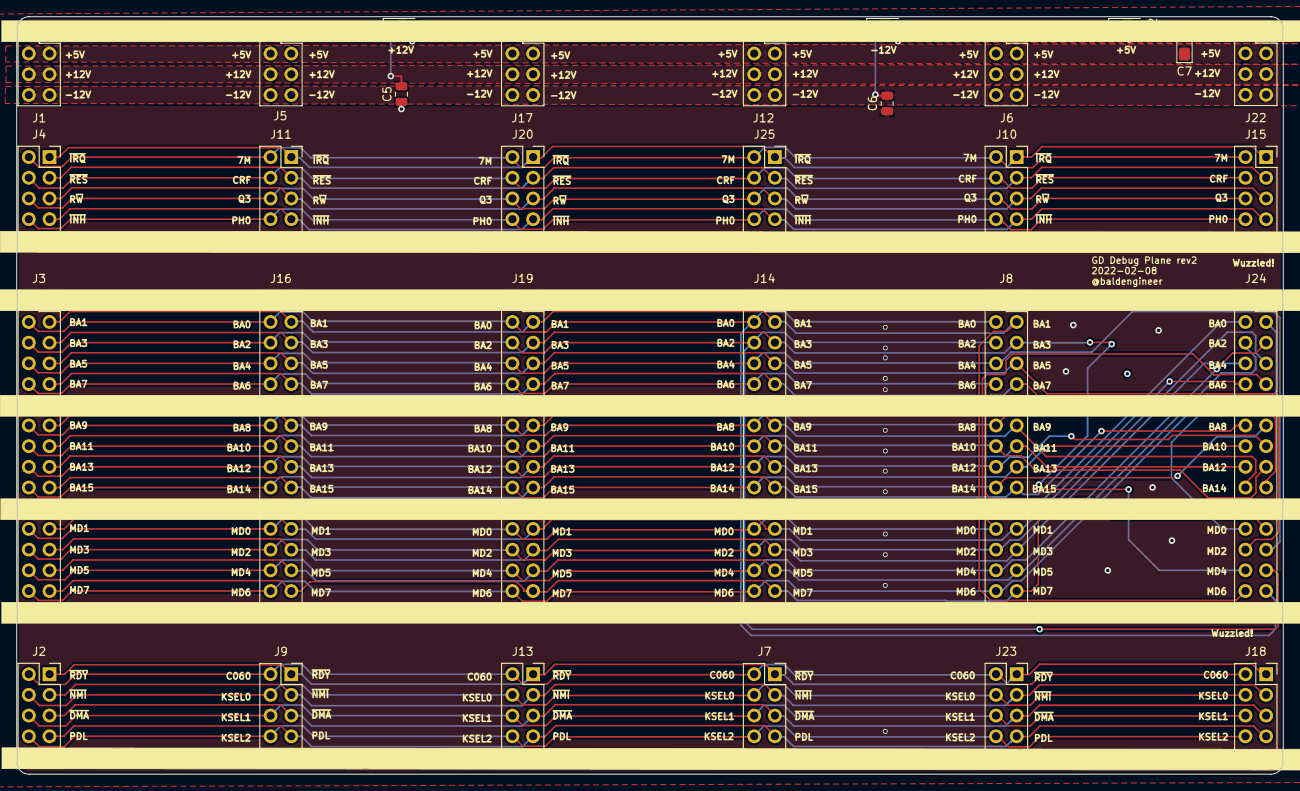
[picture p82: board gd blackplane proto pcb.kicad_pcb from above]

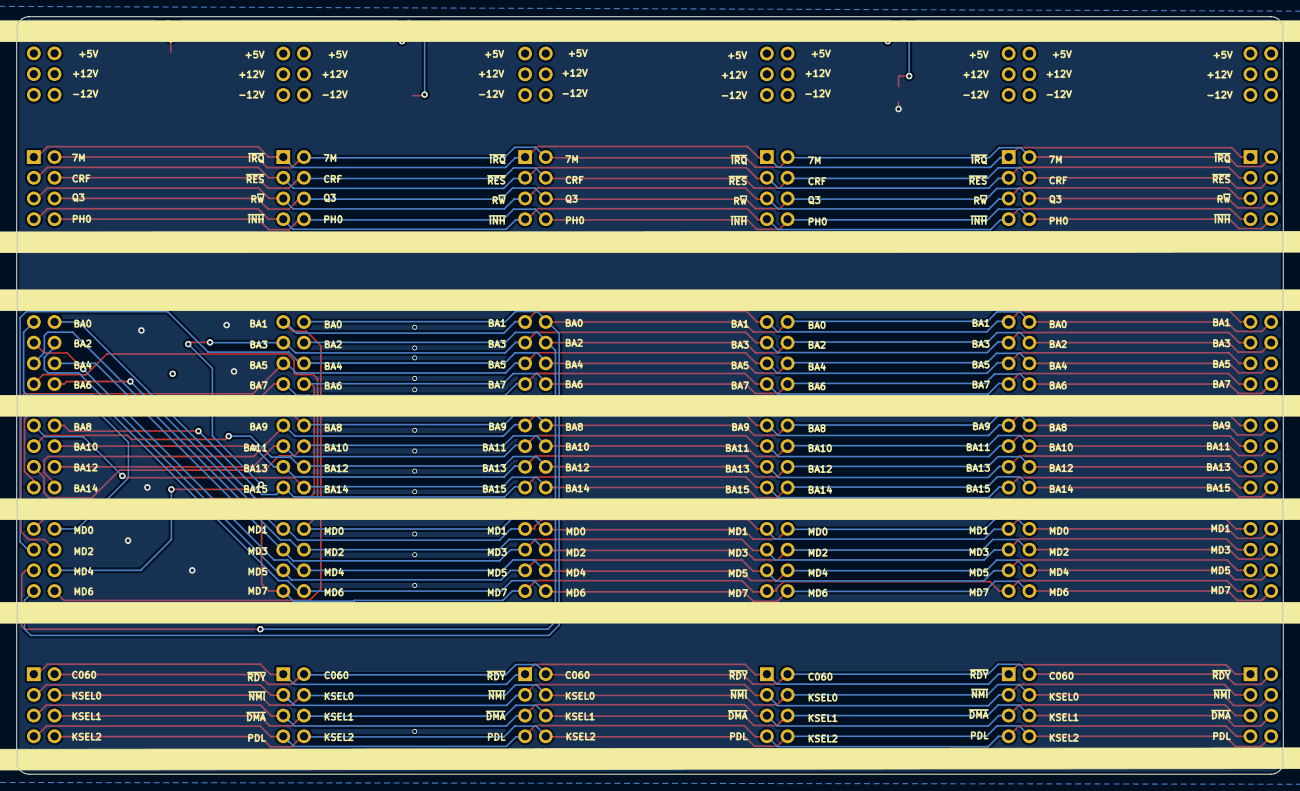
[picture p83: board gd blackplane proto pcb.kicad_pcb from below]

Board: 2 copper layers, 155.4 x 93.0 mm, 33 parts (3 on the bottom side), 47 nets.

Parts:
C5: 10uF; C_0805_2012Metric
C6: 100nF; C_0805_2012Metric
C7: 100uF; CP_EIA-3216-18_Kemet-A_Pad1.58x1.35mm_HandSolder
D1: +12; LED_1206_3216Metric
D2: +5; LED_1206_3216Metric
D3: -12; LED_1206_3216Metric
J1, J5, J6, J12, J17, J22: Pwr; PinSocket_2x04_P2.54mm_Vertical
J2, J7, J9, J13, J18, J23: CTRL2; PinSocket_2x05_P2.54mm_Vertical
J3, J8, J14, J16, J19, J24: Addr_Main_Data; PinSocket_2x16_P2.54mm_Vertical
J4, J10, J11, J15, J20, J25: CTRL1; PinSocket_2x05_P2.54mm_Vertical
R1, R2, R3: 1k; R_0805_2012Metric

Connections:
+5V: C7.1, J1.3, J1.4, J5.3, J5.4, J6.3, J6.4, J12.3, J12.4, J17.3, J17.4, J22.3, J22.4, R2.1
+12V: C5.1, J1.5, J1.6, J5.5, J5.6, J6.5, J6.6, J12.5, J12.6, J17.5, J17.6, J22.5, J22.6, R1.1
-12V: C6.1, D3.1, J1.7, J1.8, J5.7, J5.8, J6.7, J6.8, J12.7, J12.8, J17.7, J17.8, J22.7, J22.8
/7M: J4.2, J10.2, J11.2, J15.2, J20.2, J25.2
/BA0: J3.4, J8.4, J14.4, J16.4, J19.4, J24.29
/BA1: J3.3, J8.3, J14.3, J16.3, J19.3, J24.30
/BA2: J3.6, J8.6, J14.6, J16.6, J19.6, J24.27
/BA3: J3.5, J8.5, J14.5, J16.5, J19.5, J24.28
/BA4: J3.8, J8.8, J14.8, J16.8, J19.8, J24.25
/BA5: J3.7, J8.7, J14.7, J16.7, J19.7, J24.26
/BA6: J3.10, J8.10, J14.10, J16.10, J19.10, J24.23
/BA7: J3.9, J8.9, J14.9, J16.9, J19.9, J24.24
/BA8: J3.14, J8.14, J14.14, J16.14, J19.14, J24.19
/BA9: J3.13, J8.13, J14.13, J16.13, J19.13, J24.20
/BA10: J3.16, J8.16, J14.16, J16.16, J19.16, J24.17
/BA11: J3.15, J8.15, J14.15, J16.15, J19.15, J24.18
/BA12: J3.18, J8.18, J14.18, J16.18, J19.18, J24.15
/BA13: J3.17, J8.17, J14.17, J16.17, J19.17, J24.16
/BA14: J3.20, J8.20, J14.20, J16.20, J19.20, J24.13
/BA15: J3.19, J8.19, J14.19, J16.19, J19.19, J24.14
/C060-67: J2.2, J7.2, J9.2, J13.2, J18.2, J23.2
/CREF: J4.4, J10.4, J11.4, J15.4, J20.4, J25.4
/KSEL0: J2.4, J7.4, J9.4, J13.4, J18.4, J23.4
/KSEL1: J2.6, J7.6, J9.6, J13.6, J18.6, J23.6
/KSEL2: J2.8, J7.8, J9.8, J13.8, J18.8, J23.8
/MD0: J3.24, J8.24, J14.24, J16.24, J19.24, J24.9
/MD1: J3.23, J8.23, J14.23, J16.23, J19.23, J24.10
/MD2: J3.26, J8.26, J14.26, J16.26, J19.26, J24.7
/MD3: J3.25, J8.25, J14.25, J16.25, J19.25, J24.8
/MD4: J3.28, J8.28, J14.28, J16.28, J19.28, J24.5
/MD5: J3.27, J8.27, J14.27, J16.27, J19.27, J24.6
/MD6: J3.30, J8.30, J14.30, J16.30, J19.30, J24.3
/MD7: J3.29, J8.29, J14.29, J16.29, J19.29, J24.4
/PDLTRIG: J2.7, J7.7, J9.7, J13.7, J18.7, J23.7
/PH0: J4.8, J10.8, J11.8, J15.8, J20.8, J25.8
/Q3: J4.6, J10.6, J11.6, J15.6, J20.6, J25.6
/RW: J4.5, J10.5, J11.5, J15.5, J20.5, J25.5
/~DMA: J2.5, J7.5, J9.5, J13.5, J18.5, J23.5
/~INH: J4.7, J10.7, J11.7, J15.7, J20.7, J25.7
/~IRQ: J4.1, J10.1, J11.1, J15.1, J20.1, J25.1
/~NMI: J2.3, J7.3, J9.3, J13.3, J18.3, J23.3
/~RDY: J2.1, J7.1, J9.1, J13.1, J18.1, J23.1
/~RESET: J4.3, J10.3, J11.3, J15.3, J20.3, J25.3
GND: C5.2, C6.2, C7.2, D1.1, D2.1, J1.1, J1.2, J2.9, J2.10, J3.1, J3.2, J3.11, J3.12, J3.21, J3.22, J3.31, J3.32, J4.9, J4.10, J5.1, J5.2, J6.1, J6.2, J7.9, J7.10, J8.1, J8.2, J8.11, J8.12, J8.21, J8.22, J8.31, J8.32, J9.9, J9.10, J10.9, J10.10, J11.9, J11.10, J12.1, J12.2, J13.9, J13.10, J14.1, J14.2, J14.11, J14.12, J14.21, J14.22, J14.31, J14.32, J15.9, J15.10, J16.1, J16.2, J16.11, J16.12, J16.21, J16.22, J16.31, J16.32, J17.1, J17.2, J18.9, J18.10, J19.1, J19.2, J19.11, J19.12, J19.21, J19.22, J19.31, J19.32, J20.9, J20.10, J22.1, J22.2, J23.9, J23.10, J24.1, J24.2, J24.11, J24.12, J24.21, J24.22, J24.31, J24.32, J25.9, J25.10, R3.2
unnamed: D1.2, R1.2
unnamed: D2.2, R2.2
unnamed: D3.2, R3.1
