baldengineer/Mega-IIe/kicad files/gd rev2 crystalposer/gd rev2 crystalposer.kicad_pcb

## KiCad design kicad files/gd rev2 crystalposer/gd rev2 crystalposer.kicad_pcb (2022-01-31)

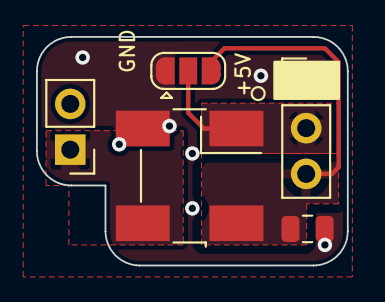
[picture p84: board gd rev2 crystalposer.kicad_pcb from above]

Board: 2 copper layers, 17.3 x 12.7 mm, 5 parts (0 on the bottom side), 4 nets.

Parts:
C1: 1uF; C_0805_2012Metric
J1: 14M Enable; PinHeader_1x03_P2.54mm_Vertical
J2: 14M_SEL; PinHeader_1x02_P2.54mm_Vertical
JP1: X_EN; SolderJumper-3_P1.3mm_Open_RoundedPad1.0x1.5mm
X1: 14.31818MHz; Oscillator_MCP_SMD_7050

Connections:
+5V: C1.1, J1.3, JP1.3 (B), X1.4 (V+)
/14M: J2.1, X1.3 (OUT)
/EN: J1.2, JP1.2 (C), X1.1 (EN)
GND: C1.2, J1.1, JP1.1 (A), X1.2 (GND)
