baldengineer/Mega-IIe/kicad files/servid-rp2040-hdmi proto rev1/servid-rp2040-hdmi proto rev1.kicad_pcb

## KiCad design kicad files/servid-rp2040-hdmi proto rev1/servid-rp2040-hdmi proto rev1.kicad_pcb (2021-12-31)

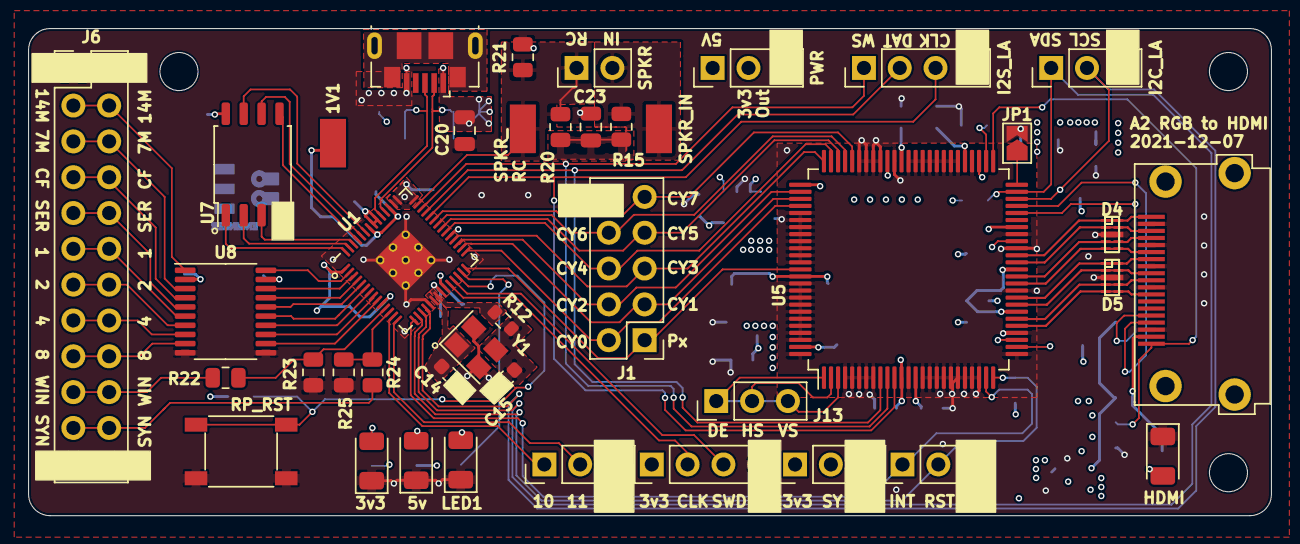
[picture p85: board servid-rp2040-hdmi proto rev1.kicad_pcb from above]

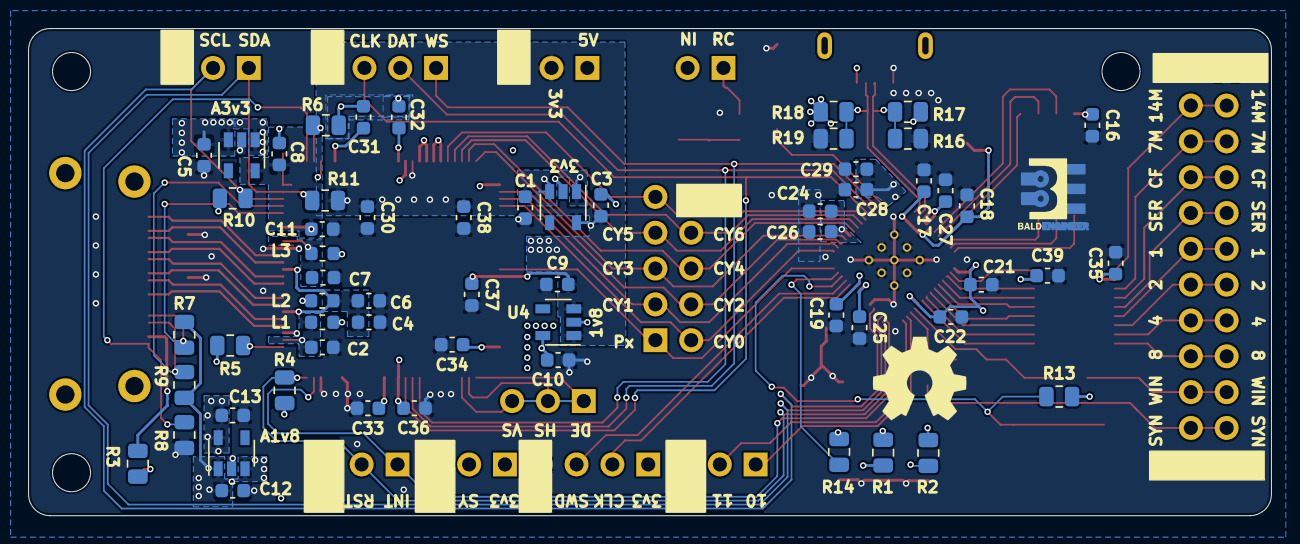
[picture p86: board servid-rp2040-hdmi proto rev1.kicad_pcb from below]

Board: 4 copper layers, 88.1 x 34.5 mm, 104 parts (60 on the bottom side), 88 nets.

Parts:
C1, C5, C9, C12, C19, C21, C35, C39: 1u; C_0603_1608Metric
C2, C3, C4, C6, C7, C8, C10, C11, C13, C16, C17, C18, C22, C24, C25, C26, C27, C28, C29, C30, C31, C32, C33, C34, C36, C37, C38: 100n; C_0603_1608Metric
C14, C15: 27p; C_0603_1608Metric
C20: 10u; C_0805_2012Metric
C23: 100n; C_0805_2012Metric
D1: 5v; LED_1206_3216Metric
D2: 3v3; LED_1206_3216Metric
D3: HDMI; LED_1206_3216Metric
D4, D5: RClamp0524P; SLP2510P8
D6: LED1; LED_1206_3216Metric
H1, H3, H4: MountingHole; MountingHole_2.7mm_M2.5
J1: ITU-656; PinHeader_2x05_P2.54mm_Vertical
J2: INT_LA; PinHeader_1x03_P2.54mm_Vertical
J3: I2C_LA; PinHeader_1x03_P2.54mm_Vertical
J4: I2S_LA; PinHeader_1x04_P2.54mm_Vertical
J5: USB_B_Micro-CHECK FOOTPRINT; USB_Micro-B_GCT_USB3076-30-A
J6: VIDS; PinHeader_2x12_P2.54mm_Vertical
J7: 10029449-111RLF; 10029449
J8: SWD; PinHeader_1x04_P2.54mm_Vertical
J9: GPIO; PinHeader_1x03_P2.54mm_Vertical
J10, J13: SYNCs; PinHeader_1x03_P2.54mm_Vertical
J11: SPKR; PinHeader_1x02_P2.54mm_Vertical
J12: PWR; PinHeader_1x03_P2.54mm_Vertical
JP1: PCADR; SolderJumper-2_P1.3mm_Open_TrianglePad1.0x1.5mm
L1, L2, L3: MPZ1608S221A; L_0603_1608Metric
R1, R2, R3, R14, R20: 470; R_0805_2012Metric
R4, R7, R8, R9, R10, R11, R13: 4k7; R_0805_2012Metric
R5: 698; R_0805_2012Metric
R6, R21: 1k; R_0805_2012Metric
R12: 1k; R_0603_1608Metric
R15: 100; R_0805_2012Metric
R16, R18: 75k; R_0805_2012Metric
R17, R19: 49.9k; R_0805_2012Metric
R22, R24: 22k; R_0805_2012Metric
R23, R25: 47k; R_0805_2012Metric
SW1: RP_RST; SW_Push_CK_PTS525_SM15
TP1: TP_1v1; Harwin-S1751-46-Test-Point
TP2: TP_SPKR_IN; Harwin-S1751-46-Test-Point
TP4: TP_SPKR_RC; Harwin-S1751-46-Test-Point
U1: RP2040; RP2040-QFN-56
U2, U3: MIC5504-3.3YM5; SOT-23-5
U4, U6: MIC5504-1.8YM5; SOT-23-5
U5: IT6613; LQFP-100_14x14mm_P0.5mm
U7: W25Q128JVS; SOIC-8_5.23x5.23mm_P1.27mm
U8: TXB0108PW; TSSOP-20_4.4x6.5mm_P0.65mm
Y1: ECS-120-18-33-JEM; Crystal_SMD_3225-4Pin_3.2x2.5mm
svg2mod: G***; BE5v2

Connections:
+1V1: C17.1, C18.1, C19.1, TP1.1, U1.23, U1.45, U1.50
+1V8: C10.1, C31.1, C32.1, C34.1, C36.1, U4.5, U5.12, U5.55, U5.64, U5.76, U5.99
+3V3: C3.1, C9.1, C16.1, C21.1, C22.1, C24.1, C25.1, C26.1, C27.1, C28.1, C29.1, C30.1, C33.1, C37.1, C38.1, C39.1, J8.1, J10.1, J12.2, R2.1, R4.1, R10.1, R11.1, R13.2, U1.1, U1.10, U1.22, U1.33, U1.42, U1.43, U1.44, U1.48, U1.49, U2.5, U4.1, U4.3, U5.14, U5.53, U5.66, U5.89, U7.8, U8.19
+5V: C1.1, C5.1, C12.1, C20.1, C35.1, J5.1, J12.1, R1.1, R7.1, R9.1, R16.1, R18.1, U2.1, U2.3, U3.1, U3.3, U6.1, U6.3, U8.2
/7M: J6.5, J6.6, U8.3
/14M: J6.3, J6.4, U8.1
/A1v8: C13.1, L1.1, L2.1, L3.1, R5.2, U6.5
/A3v3: C8.1, C11.1, U3.5, U5.44
/AVCC18: C4.1, C6.1, L2.2, U5.32, U5.38
/CREF: J6.7, J6.8, U8.4
/CY0: J1.2, U1.29, U5.79
/CY1: J1.3, U1.30, U5.78
/CY2: J1.4, U1.31, U5.77
/CY3: J1.5, U1.32, U5.75
/CY4: J1.6, U1.34, U5.74
/CY5: J1.7, U1.35, U5.73
/CY6: J1.8, U1.36, U5.72
/CY7: J1.9, U1.37, U5.71
/DDC_SCL: J7.15, R7.2, U5.46
/DDC_SDA: J7.16, R9.2, U5.47
/DE: J13.1, U5.1
/GPIO10: J9.1, U1.13
/GPIO11: J9.2, U1.14
/HDMI_5V: J7.18, R3.1
/HPD: J7.19, R8.2, U5.51
/HSYNC: J13.2, U5.2
/I2C_SCL: J3.2, R10.2, U1.18, U5.48
/I2C_SDA: J3.1, R11.2, U1.17, U5.49
/INT#: J2.1, U1.15, U5.24
/IT_RST#: J2.2, R4.2, U1.16, U5.25
/LED1: R14.1, U1.27
/PCADR: JP1.1, U5.50
/PIO_I2S_CLK: J4.3, U1.38, U5.11
/PIO_I2S_DATA: J4.2, U1.39, U5.9
/PIO_I2S_WS: J4.1, U1.40, U5.10
/PVCC1: C2.1, L1.2, U5.28
/PVCC2: C7.1, L3.2, U5.42
/PxCLK: J1.1, U1.28, U5.88
/QSPI_SCLK: U1.52, U7.6
/QSPI_SD0: U1.53, U7.5
/QSPI_SD1: U1.55, U7.2
/QSPI_SD2: U1.54, U7.3
/QSPI_SD3: U1.51, U7.7
/QSPI_SS: U1.56, U7.1
/RGB1: J6.11, J6.12, U8.6
/RGB2: J6.13, J6.14, U8.7
/RGB4: J6.15, J6.16, U8.8
/RGB8: J6.17, J6.18, U8.9
/Run: R13.1, SW1.2, U1.26
/SERVID: J6.9, J6.10, U8.5
/SPKR_IN: J11.2, R15.1, TP2.1
/SPKR_RC: J11.1, R20.1, R21.1, TP4.1, U1.41
/SWCLK: J8.2, U1.24
/SWD: J8.3, U1.25
/TMDS_CLK+: D5.4, D5.7, J7.10, U5.31
/TMDS_CLK-: D5.5, D5.6, J7.12, U5.30
/TMDS_D0+: D5.1, D5.10, J7.7, U5.34
/TMDS_D0-: D5.2, D5.9, J7.9, U5.33
/TMDS_D1+: D4.4, D4.7, J7.4, U5.37
/TMDS_D1-: D4.5, D4.6, J7.6, U5.36
/TMDS_D2+: D4.1, D4.10, J7.1, U5.40
/TMDS_D2-: D4.2, D4.9, J7.3, U5.39
/USB_DM: J5.2, R18.2, R19.1, U1.46
/USB_DP: J5.3, R16.2, R17.1, U1.47
/VSYNC: J13.3, U5.3
/XIN: C14.1, U1.20, Y1.1
/XOUT: R12.2, U1.21
/b7M: U1.3, U8.18
/b14M: U1.2, U8.20
/bCREF: U1.4, U8.17
/bRGB1: U1.6, U8.15
/bRGB2: U1.7, U8.14
/bRGB4: U1.8, U8.13
/bRGB8: U1.9, U8.12
/bSERVID: U1.5, U8.16
/~SYNC: J6.21, J6.22, R24.1
/~WINDOW: J6.19, J6.20, R22.1
/~bSYNC: R24.2, R25.1, U1.12
/~bWINDOW: R22.2, R23.1, U1.11
GND: C1.2, C2.2, C3.2, C4.2, C5.2, C6.2, C7.2, C8.2, C9.2, C10.2, C11.2, C12.2, C13.2, C14.2, C15.2, C16.2, C17.2, C18.2, C19.2, C20.2, C21.2, C22.2, C23.2, C24.2, C25.2, C26.2, C27.2, C28.2, C29.2, C30.2, C31.2, C32.2, C33.2, C34.2, C35.2, C36.2, C37.2, C38.2, C39.2, D1.1, D2.1, D3.1, D4.3, D4.8, D5.3, D5.8, D6.1, J1.10, J2.3, J3.3, J4.4, J5.5, J6.1, J6.2, J6.23, J6.24, J7.2, J7.5, J7.8, J7.11, J7.17, J8.4, J9.3, J10.3, J12.3, JP1.2, R6.1, R8.1, R17.2, R19.2, R21.2, R23.2, R25.2, SW1.1, U1.19, U1.57, U2.2, U3.2, U4.2, U5.4, U5.5, U5.6, U5.7, U5.8, U5.13, U5.15, U5.16, U5.17, U5.18, U5.19, U5.20, U5.21, U5.22, U5.23, U5.26, U5.29, U5.35, U5.41, U5.43, U5.54, U5.56, U5.57, U5.58, U5.59, U5.60, U5.61, U5.62, U5.63, U5.65, U5.67, U5.68, U5.69, U5.70, U5.80, U5.81, U5.82, U5.83, U5.84, U5.85, U5.86, U5.87, U5.90, U5.91, U5.92, U5.93, U5.94, U5.95, U5.96, U5.97, U5.98, U5.100, U6.2, U7.4, U8.10, U8.11, Y1.2, Y1.4
unnamed: C15.1, R12.1, Y1.3
unnamed: C23.1, R15.2, R20.2
unnamed: D1.2, R1.2
unnamed: D2.2, R2.2
unnamed: D3.2, R3.2
unnamed: D6.2, R14.2
unnamed: R5.1, U5.27
unnamed: R6.2, U5.52
