baldengineer/Mega-IIe/kicad files/gd interdeswizzlepozer pcb/gd interdeswizzlepozer.kicad_pcb

## KiCad design kicad files/gd interdeswizzlepozer pcb/gd interdeswizzlepozer.kicad_pcb (2021-12-31)

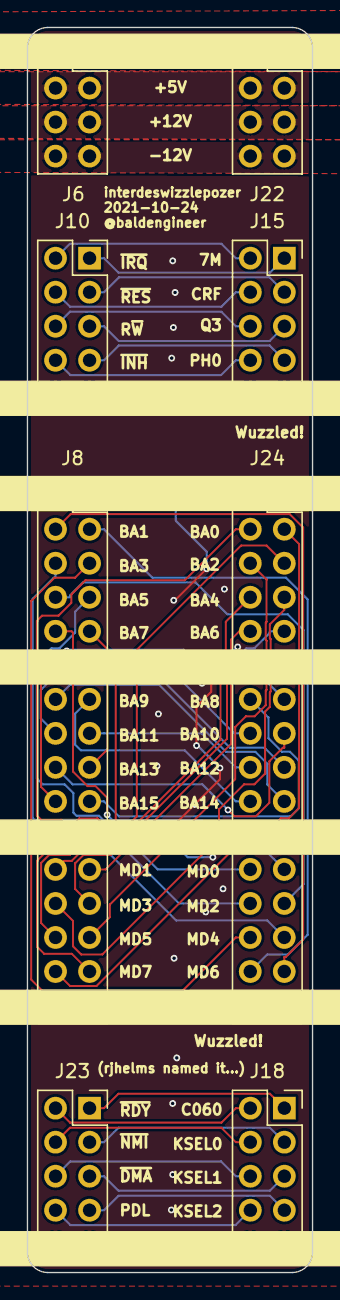
[picture p87: board gd interdeswizzlepozer.kicad_pcb from above]

Board: 2 copper layers, 21.3 x 93.0 mm, 8 parts (0 on the bottom side), 44 nets.

Parts:
J6, J22: Pwr; PinSocket_2x04_P2.54mm_Vertical
J8, J24: Addr_Main_Data; PinSocket_2x16_P2.54mm_Vertical
J10, J15: CTRL1; PinSocket_2x05_P2.54mm_Vertical
J18, J23: CTRL2; PinSocket_2x05_P2.54mm_Vertical

Connections:
+5V: J6.3, J6.4, J22.3, J22.4
+12V: J6.5, J6.6, J22.5, J22.6
-12V: J6.7, J6.8, J22.7, J22.8
/7M: J10.2, J15.2
/BA0: J8.4, J24.29
/BA1: J8.3, J24.30
/BA2: J8.6, J24.27
/BA3: J8.5, J24.28
/BA4: J8.8, J24.25
/BA5: J8.7, J24.26
/BA6: J8.10, J24.23
/BA7: J8.9, J24.24
/BA8: J8.14, J24.19
/BA9: J8.13, J24.20
/BA10: J8.16, J24.17
/BA11: J8.15, J24.18
/BA12: J8.18, J24.15
/BA13: J8.17, J24.16
/BA14: J8.20, J24.13
/BA15: J8.19, J24.14
/C060-67: J18.2, J23.2
/CREF: J10.4, J15.4
/GND: J6.1, J6.2, J8.1, J8.2, J8.11, J8.12, J8.21, J8.22, J8.31, J8.32, J10.9, J10.10, J15.9, J15.10, J18.9, J18.10, J22.1, J22.2, J23.9, J23.10, J24.1, J24.2, J24.11, J24.12, J24.21, J24.22, J24.31, J24.32
/KSEL0: J18.4, J23.4
/KSEL1: J18.6, J23.6
/KSEL2: J18.8, J23.8
/MD0: J8.24, J24.9
/MD1: J8.23, J24.10
/MD2: J8.26, J24.7
/MD3: J8.25, J24.8
/MD4: J8.28, J24.5
/MD5: J8.27, J24.6
/MD6: J8.30, J24.3
/MD7: J8.29, J24.4
/PDLTRIG: J18.7, J23.7
/PH0: J10.8, J15.8
/Q3: J10.6, J15.6
/RW: J10.5, J15.5
/~DMA: J18.5, J23.5
/~INH: J10.7, J15.7
/~IRQ: J10.1, J15.1
/~NMI: J18.3, J23.3
/~RDY: J18.1, J23.1
/~RESET: J10.3, J15.3
