baldengineer/Mega-IIe/kicad files/not_used/gd rev2 backplane/gd rev2 backplane.kicad_pcb

## KiCad design kicad files/not_used/gd rev2 backplane/gd rev2 backplane.kicad_pcb (2021-08-15)

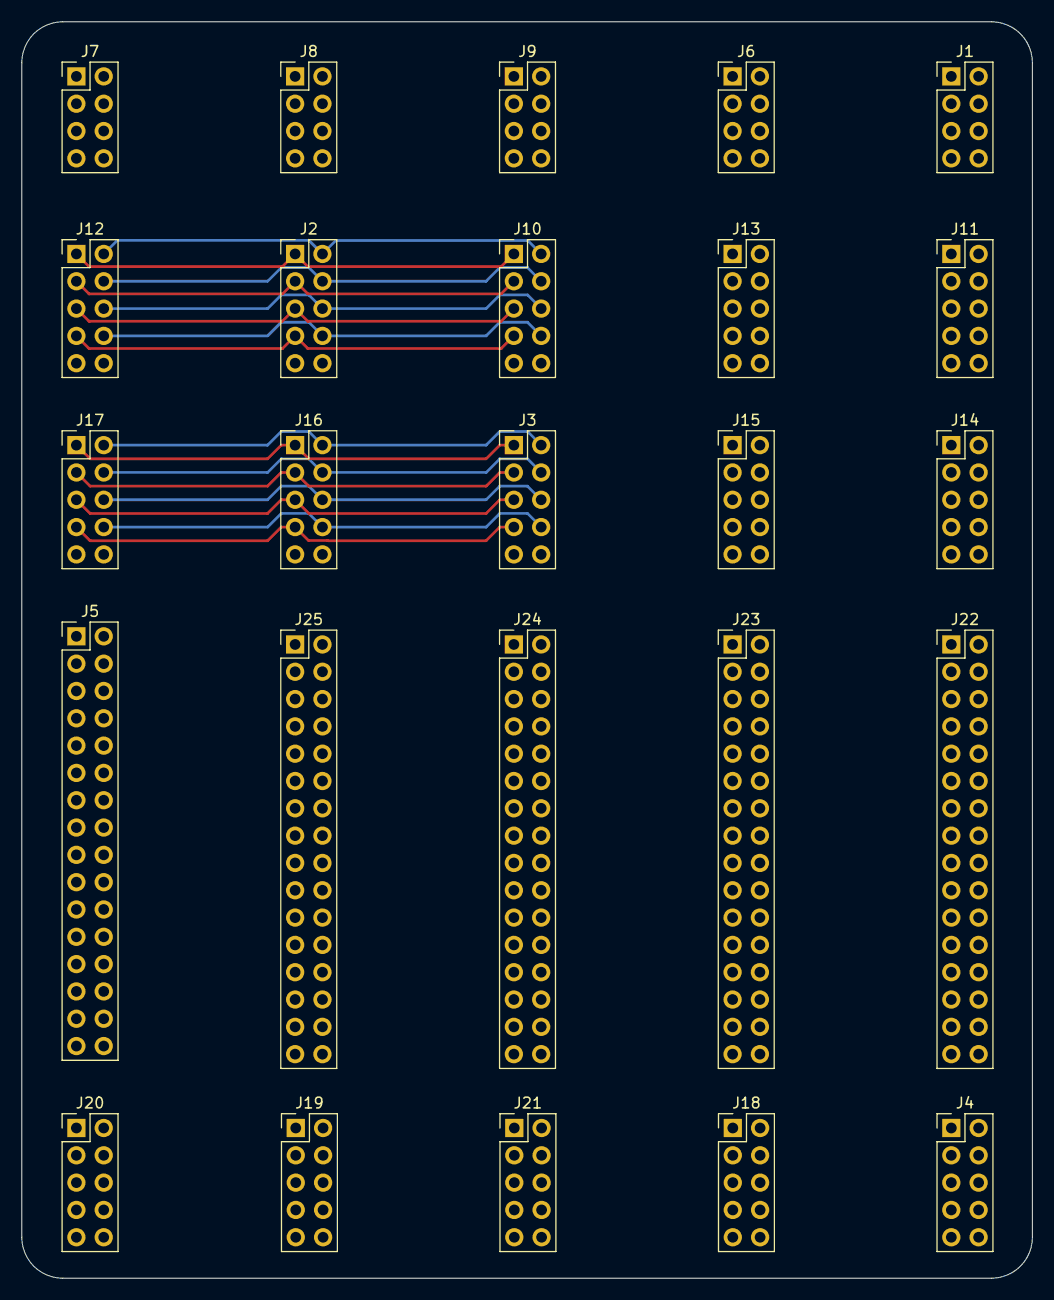
[picture p88: board gd rev2 backplane.kicad_pcb from above]

Board: 2 copper layers, 94.0 x 116.8 mm, 25 parts (0 on the bottom side), 52 nets.

Parts:
J1, J6, J7, J8, J9: Pwr; PinHeader_2x04_P2.54mm_Vertical
J2, J10, J11, J12, J13: Slot_Maker; PinHeader_2x05_P2.54mm_Vertical
J3, J14, J15, J16, J17: CTRL2; PinHeader_2x05_P2.54mm_Vertical
J4, J18, J19, J20, J21: CTRL1; PinHeader_2x05_P2.54mm_Vertical
J5, J22, J23, J24, J25: Addr_Main_Data; PinHeader_2x16_P2.54mm_Vertical

Connections:
+5V: J1.1, J1.3, J6.1, J6.3, J7.1, J7.3, J8.1, J8.3, J9.1, J9.3
+12V: J1.5, J1.7, J6.5, J6.7, J7.5, J7.7, J8.5, J8.7, J9.5, J9.7
-12V: J1.6, J1.8, J6.6, J6.8, J7.6, J7.8, J8.6, J8.8, J9.6, J9.8
/7M: J4.2, J18.2, J19.2, J20.2, J21.2
/!DMA: J3.5, J14.5, J15.5, J16.5, J17.5
/BA0: J5.4, J22.4, J23.4, J24.4, J25.4
/BA1: J5.3, J22.3, J23.3, J24.3, J25.3
/BA2: J5.6, J22.6, J23.6, J24.6, J25.6
/BA3: J5.5, J22.5, J23.5, J24.5, J25.5
/BA4: J5.8, J22.8, J23.8, J24.8, J25.8
/BA5: J5.7, J22.7, J23.7, J24.7, J25.7
/BA6: J5.10, J22.10, J23.10, J24.10, J25.10
/BA7: J5.9, J22.9, J23.9, J24.9, J25.9
/BA8: J5.14, J22.14, J23.14, J24.14, J25.14
/BA9: J5.13, J22.13, J23.13, J24.13, J25.13
/BA10: J5.16, J22.16, J23.16, J24.16, J25.16
/BA11: J5.15, J22.15, J23.15, J24.15, J25.15
/BA12: J5.18, J22.18, J23.18, J24.18, J25.18
/BA13: J5.17, J22.17, J23.17, J24.17, J25.17
/BA14: J5.20, J22.20, J23.20, J24.20, J25.20
/BA15: J5.19, J22.19, J23.19, J24.19, J25.19
/C060-67: J3.2, J14.2, J15.2, J16.2, J17.2
/CREF: J4.4, J18.4, J19.4, J20.4, J21.4
/GND: J1.2, J1.4, J2.9, J2.10, J3.9, J3.10, J4.9, J4.10, J5.1, J5.2, J5.11, J5.12, J5.21, J5.22, J5.31, J5.32, J6.2, J6.4, J7.2, J7.4, J8.2, J8.4, J9.2, J9.4, J10.9, J10.10, J11.9, J11.10, J12.9, J12.10, J13.9, J13.10, J14.9, J14.10, J15.9, J15.10, J16.9, J16.10, J17.9, J17.10, J18.9, J18.10, J19.9, J19.10, J20.9, J20.10, J21.9, J21.10, J22.1, J22.2, J22.11, J22.12, J22.21, J22.22, J22.31, J22.32, J23.1, J23.2, J23.11, J23.12, J23.21, J23.22, J23.31, J23.32, J24.1, J24.2, J24.11, J24.12, J24.21, J24.22, J24.31, J24.32, J25.1, J25.2, J25.11, J25.12, J25.21, J25.22, J25.31, J25.32
/INTDEV6: J2.8, J10.8, J11.8, J12.8, J13.8
/KSEL0: J3.4, J14.4, J15.4, J16.4, J17.4
/KSEL1: J3.6, J14.6, J15.6, J16.6, J17.6
/KSEL2: J3.8, J14.8, J15.8, J16.8, J17.8
/MD0: J5.24, J22.24, J23.24, J24.24, J25.24
/MD1: J5.23, J22.23, J23.23, J24.23, J25.23
/MD2: J5.26, J22.26, J23.26, J24.26, J25.26
/MD3: J5.25, J22.25, J23.25, J24.25, J25.25
/MD4: J5.28, J22.28, J23.28, J24.28, J25.28
/MD5: J5.27, J22.27, J23.27, J24.27, J25.27
/MD6: J5.30, J22.30, J23.30, J24.30, J25.30
/MD7: J5.29, J22.29, J23.29, J24.29, J25.29
/MDI-MDO: J2.7, J10.7, J11.7, J12.7, J13.7
/PDLTRIG: J3.7, J14.7, J15.7, J16.7, J17.7
/PH0: J4.8, J18.8, J19.8, J20.8, J21.8
/Q3: J4.6, J18.6, J19.6, J20.6, J21.6
/RW: J4.5, J18.5, J19.5, J20.5, J21.5
/S0: J2.2, J10.2, J11.2, J12.2, J13.2
/S1: J2.1, J10.1, J11.1, J12.1, J13.1
/S2: J2.4, J10.4, J11.4, J12.4, J13.4
/S3: J2.3, J10.3, J11.3, J12.3, J13.3
/S4: J2.6, J10.6, J11.6, J12.6, J13.6
/S5: J2.5, J10.5, J11.5, J12.5, J13.5
/~INH: J4.7, J18.7, J19.7, J20.7, J21.7
/~IRQ: J4.1, J18.1, J19.1, J20.1, J21.1
/~NMI: J3.3, J14.3, J15.3, J16.3, J17.3
/~RDY: J3.1, J14.1, J15.1, J16.1, J17.1
/~RESET: J4.3, J18.3, J19.3, J20.3, J21.3
