baldengineer/Mega-IIe/kicad files/rev1/gd MegaII proto pcb/gd MegaII proto pcb.kicad_pcb

## KiCad design kicad files/rev1/gd MegaII proto pcb/gd MegaII proto pcb.kicad_pcb (2021-06-15)

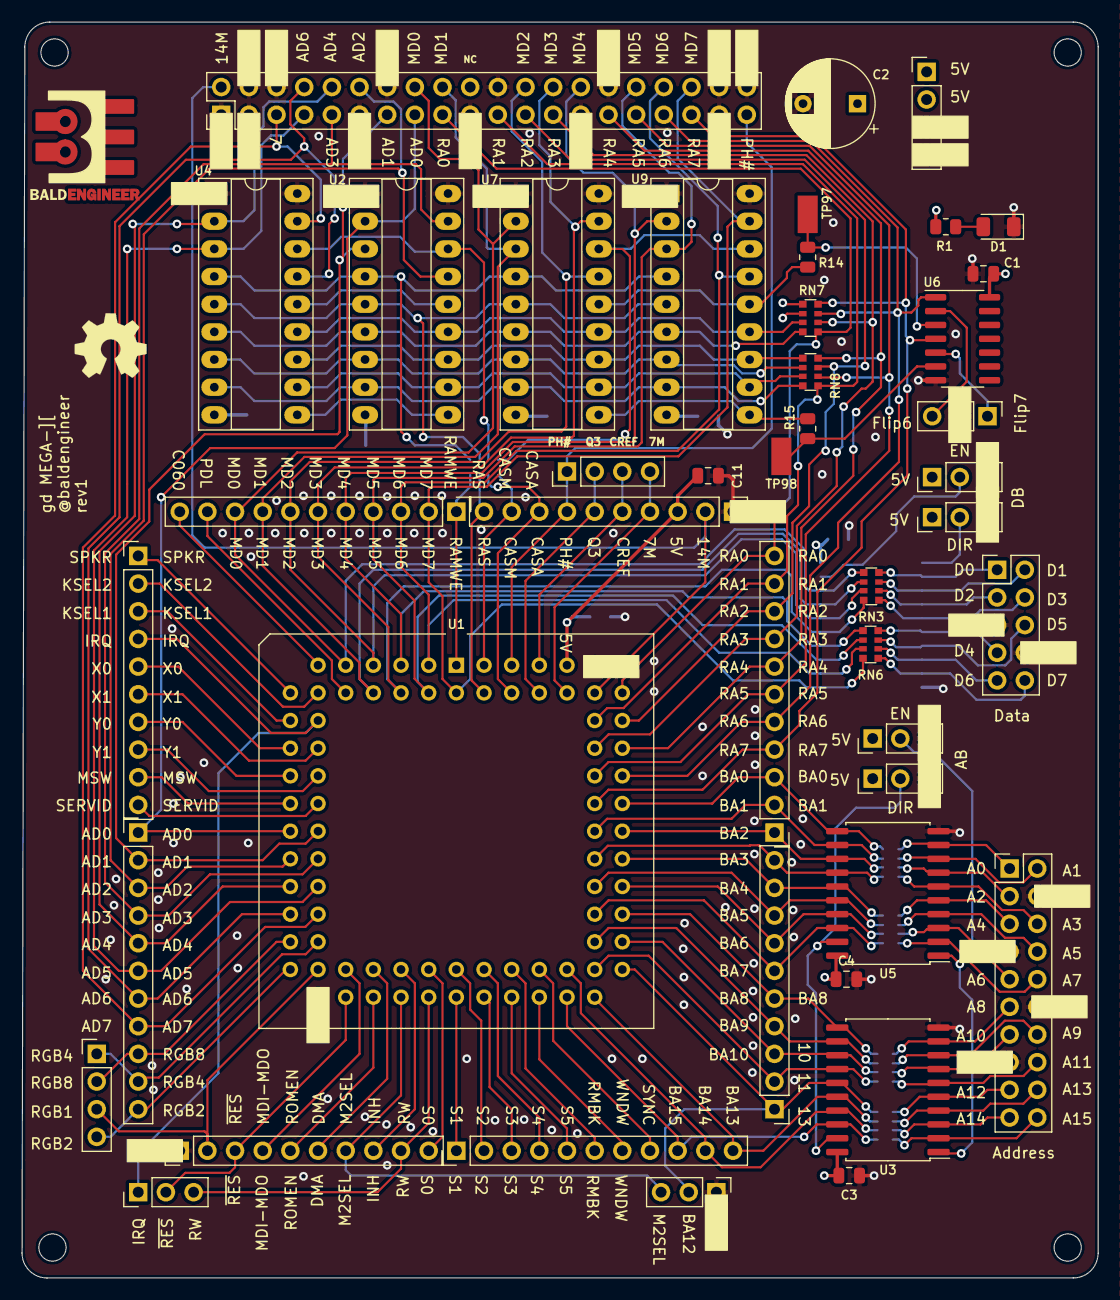
[picture p89: board gd MegaII proto pcb.kicad_pcb from above]

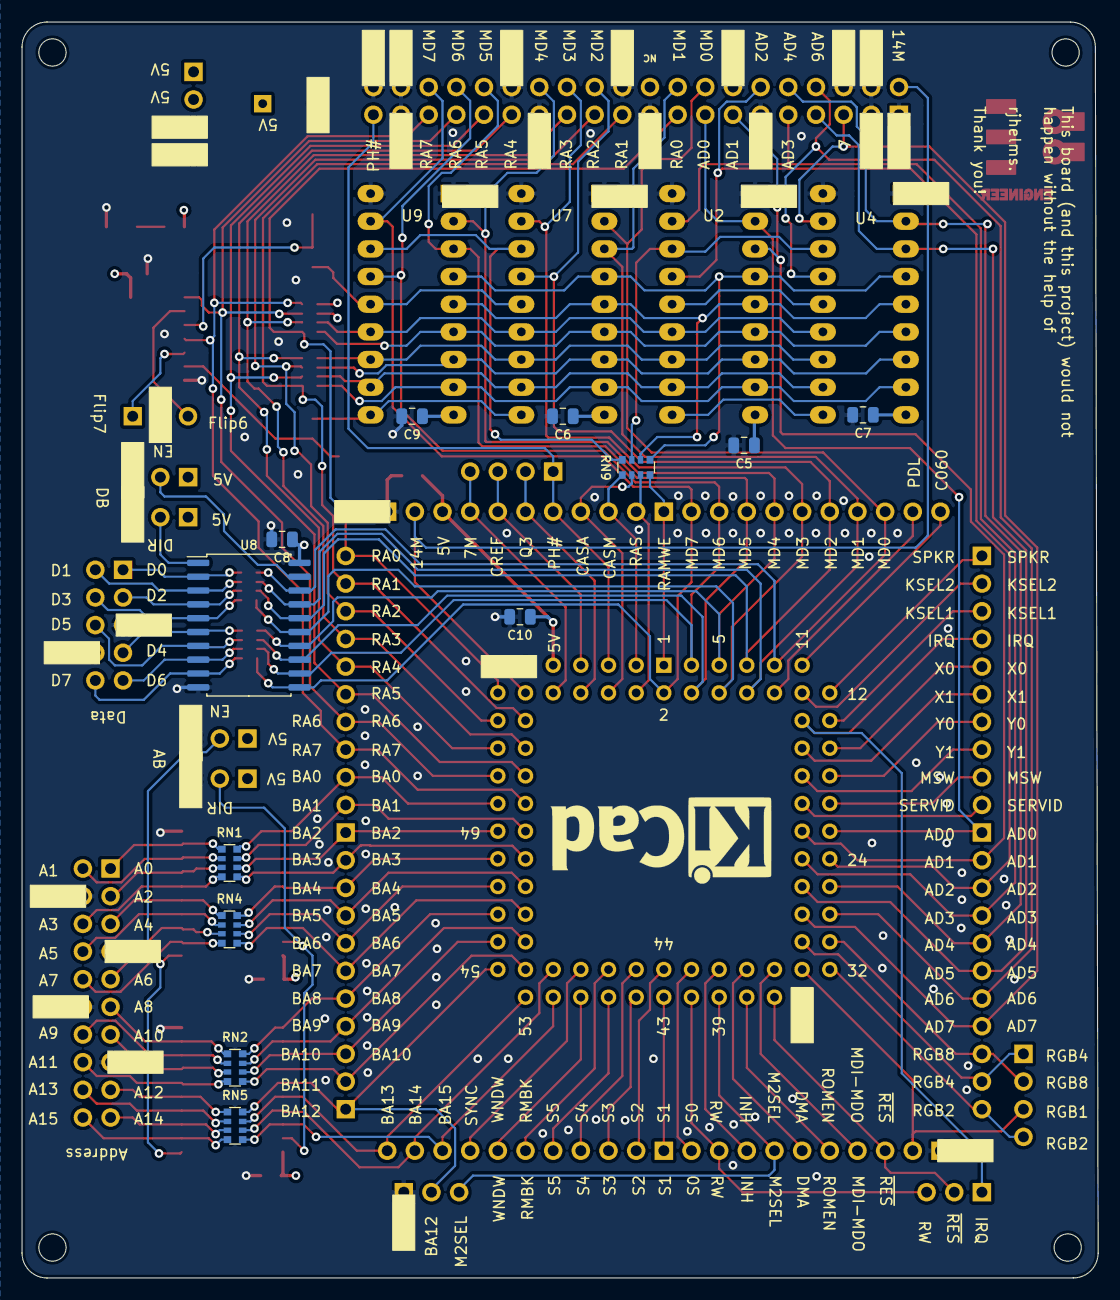
[picture p90: board gd MegaII proto pcb.kicad_pcb from below]

Board: 4 copper layers, 98.8 x 115.3 mm, 61 parts (12 on the bottom side), 130 nets.

Parts:
C1: 100nF; C_0805_2012Metric
C2: 100uF; CP_Radial_D8.0mm_P5.00mm
C3, C4, C5, C6, C7, C8, C9, C11: 1uF; C_0805_2012Metric
C10: 10uF; C_0805_2012Metric
D1: PWR; LED_1206_3216Metric
H1, H2, H3, H4: MountingHole; MountingHole_2.5mm
J1: ABDIR; PinHeader_1x03_P2.54mm_Vertical
J2: ABEN; PinHeader_1x03_P2.54mm_Vertical
J3: FLIP; PinHeader_1x03_P2.54mm_Vertical
J4: DBDIR; PinHeader_1x03_P2.54mm_Vertical
J5: DBEN; PinHeader_1x03_P2.54mm_Vertical
J6: VGC Extra 1; PinHeader_1x03_P2.54mm_Vertical
J7: Bald-Ext-1; PinHeader_2x20_P2.54mm_Vertical
J8: VGC Extra 2; PinHeader_1x03_P2.54mm_Vertical
J9: Address; PinHeader_2x10_P2.54mm_Vertical
J10: Data; PinHeader_2x05_P2.54mm_Vertical
J11: PWR; PinHeader_1x04_P2.54mm_Vertical
J12: CLKS; PinHeader_1x04_P2.54mm_Vertical
JP1: RGB Binary; PinHeader_1x04_P2.54mm_Vertical
JP3, JP7, JP12, JP16: P54-63; PinHeader_1x10_P2.54mm_Vertical
JP4, JP8, JP11, JP15: P64-74; PinHeader_1x11_P2.54mm_Vertical
R1: 1k; R_0805_2012Metric
R14, R15: 100; R_0805_2012Metric
RN1, RN2, RN3, RN4, RN5, RN6: R_Pack04; R_Array_Convex_4x0612
RN7, RN8, RN9: 100; R_Array_Convex_4x0612
TP97, TP98: TestPoint; Harwin-S1751-46-Test-Point
U1: Apple_MEGA_II; PLCC-84_THT-Socket
U2, U4, U7, U9: DRAM64KX4; DIP-18_W7.62mm_Socket_LongPads
U3, U5, U8: 74HCT245; SOIC-20W_7.5x12.8mm_P1.27mm
U6: 74HCT86; SOIC-14_3.9x8.7mm_P1.27mm
svg2mod: G***; BE10v2

Connections:
+5V: C1.1, C2.1, C3.1, C4.1, C5.1, C6.1, C7.1, C8.1, C9.1, C10.1, C11.1, J1.1, J2.1, J4.1, J5.1, J11.1, J11.2, JP12.3, R1.1, U1.77, U2.9, U3.20, U4.9, U5.20, U6.14, U7.9, U8.20, U9.9
/7M: J12.4, JP12.4, U1.78
/14M: J7.2, JP12.2, U1.76
/A0: J9.1, RN1.1, U5.9
/A1: J9.2, RN1.2, U5.8
/A2: J9.3, RN1.3, U5.7
/A3: J9.6, RN1.4, U5.6
/A4: J9.5, RN4.1, U5.5
/A5: J9.8, RN4.2, U5.4
/A6: J9.9, RN4.3, U5.3
/A7: J9.10, RN4.4, U5.2
/A8: J9.11, RN2.1, U3.9
/A9: J9.14, RN2.2, U3.8
/A10: J9.13, RN2.3, U3.7
/A11: J9.16, RN2.4, U3.6
/A12: J9.17, RN5.1, U3.5
/A13: J9.18, RN5.2, U3.4
/A14: J9.19, RN5.3, U3.3
/A15: J9.20, RN5.4, U3.2
/ABDIR: J1.2, U3.1, U5.1
/ABEN: J2.2, U3.19, U5.19
/AD0: J7.15, JP4.1, U1.22, U2.2
/AD1: J7.13, JP4.2, U1.23, U2.3
/AD2: J7.12, JP4.3, U1.24, U2.15
/AD3: J7.9, JP4.4, U1.25, U2.17
/AD4: J7.10, JP4.5, U1.26, U4.2
/AD5: J7.7, JP4.6, U1.27, U4.3
/AD6: J7.8, JP4.7, U1.28, U4.15
/AD7: J7.5, JP4.8, U1.29, U4.17
/BA0: JP15.3, RN1.8, U1.66, U5.11
/BA1: JP15.2, RN1.7, U1.65, U5.12
/BA2: JP15.1, RN1.6, U1.64, U5.13
/BA3: JP16.10, RN1.5, U1.63, U5.14
/BA4: JP16.9, RN4.8, U1.62, U5.15
/BA5: JP16.8, RN4.7, U1.61, U5.16
/BA6: JP16.7, RN4.6, U1.60, U5.17
/BA7: JP16.6, RN4.5, U1.59, U5.18
/BA8: JP16.5, RN2.8, U1.58, U3.11
/BA9: JP16.4, RN2.7, U1.57, U3.12
/BA10: JP16.3, RN2.6, U1.56, U3.13
/BA11: JP16.2, RN2.5, U1.55, U3.14
/BA12: J8.2, JP16.1, RN5.8, U1.54, U3.15
/BA13: JP11.11, RN5.7, U1.53, U3.16
/BA14: JP11.10, RN5.6, U1.52, U3.17
/BA15: JP11.9, RN5.5, U1.51, U3.18
/C060-67: JP8.11, U1.11
/CASA: JP12.8, RN9.2, U1.82
/CASA.B: RN9.7, U2.16, U4.16
/CASM: JP12.9, RN9.1, U1.83
/CASM.B: RN9.8, U7.16, U9.16
/CREF: J12.3, JP12.5, U1.79
/D0: J10.1, RN3.4, U8.2
/D1: J10.2, RN3.3, U8.3
/D2: J10.3, RN3.2, U8.4
/D3: J10.4, RN3.1, U8.5
/D4: J10.7, RN6.4, U8.6
/D5: J10.6, RN6.3, U8.7
/D6: J10.9, RN6.2, U8.8
/D7: J10.10, RN6.1, U8.9
/DBDIR: J4.2, U8.1
/DBEN: J5.2, U8.19
/DMA: JP7.6, U1.38
/FLIP6: J3.3, U6.2
/FLIP7: J3.1, U6.5
/INH: JP7.8, U1.40
/IRQ: J6.1, JP3.4, U1.15
/KSEL1: JP3.2, U1.13
/KSEL2: JP3.3, U1.14
/M2SEL: J8.3, JP7.7, U1.39
/MD0: J7.16, JP8.9, RN3.5, U1.9, U7.2, U8.18
/MD1: J7.18, JP8.8, RN3.6, U1.8, U7.3, U8.17
/MD2: J7.24, JP8.7, RN3.7, U1.7, U7.15, U8.16
/MD3: J7.26, JP8.6, RN3.8, U1.6, U7.17, U8.15
/MD4: J7.28, JP8.5, RN6.5, U1.5, U8.14, U9.2
/MD5: J7.32, JP8.4, RN6.6, U1.4, U8.13, U9.3
/MD6: J7.34, JP8.3, RN6.7, U1.3, U8.12, U9.15
/MD7: J7.36, JP8.2, RN6.8, U1.2, U8.11, U9.17
/MDI-MDO: JP7.4, U1.36
/MSW: JP3.9, U1.20
/PDLTRIG: JP8.10, U1.10
/PH#: J7.39, J12.1, JP12.7, U1.81
/Q3: J12.2, JP12.6, U1.80
/R-W: J6.3, JP7.9, U1.41
/RA0: J7.17, JP15.11, RN7.1, U1.74
/RA1: J7.21, JP15.10, RN8.1, U1.73
/RA2: J7.23, JP15.9, RN8.3, U1.72
/RA3: J7.25, JP15.8, RN7.2, U1.71
/RA4: J7.29, JP15.7, RN8.4, U1.70
/RA5: J7.31, JP15.6, RN8.2, U1.69
/RA6: J7.33, JP15.5, RN7.3, U1.68, U6.1
/RA7: J7.35, JP15.4, RN7.4, U1.67, U6.4
/RAF0: RN7.8, U2.6, U4.6, U7.6, U9.6
/RAF1: RN8.8, U2.8, U4.8, U7.8, U9.8
/RAF2: RN8.6, U2.7, U4.7, U7.7, U9.7
/RAF3: RN7.7, U2.13, U4.13, U7.13, U9.13
/RAF4: RN8.5, U2.12, U4.12, U7.12, U9.12
/RAF5: RN8.7, U2.11, U4.11, U7.11, U9.11
/RAF6: RN7.6, U2.14, U4.14
/RAF7: RN7.5, U2.10, U4.10
/RAMWE: JP8.1, RN9.4, U1.1
/RAS: JP12.10, RN9.3, U1.84
/RAS.B: RN9.6, U2.5, U4.5, U7.5, U9.5
/RESET: J6.2, JP7.3, U1.35
/RGB1: JP1.3, JP7.2, U1.34
/RGB2: JP1.4, JP4.11, U1.32
/RGB4: JP1.1, JP4.10, U1.31
/RGB8: JP1.2, JP4.9, U1.30
/RMBK: JP11.6, U1.48
/ROMEN: JP7.5, U1.37
/RWE.B: RN9.5, U2.4, U4.4, U7.4, U9.4
/S0: JP7.10, U1.42
/S1: JP11.1, U1.43
/S2: JP11.2, U1.44
/S3: JP11.3, U1.45
/S4: JP11.4, U1.46
/S5: JP11.5, U1.47
/SERVIDEO: JP3.10, U1.21
/SPKR: JP3.1, U1.12
/SYNC: JP11.8, U1.50
/UM4-10: R15.1, U7.10, U9.10
/UM4-14: R14.1, U7.14, U9.14
/WINDOW: JP11.7, U1.49
/X0: JP3.5, U1.16
/X1: JP3.6, U1.17
/Y0: JP3.7, U1.18
/Y1: JP3.8, U1.19
GND: C1.2, C2.2, C3.2, C4.2, C5.2, C6.2, C7.2, C8.2, C9.2, C10.2, C11.2, D1.1, J1.3, J2.3, J3.2, J4.3, J5.3, J7.1, J7.3, J7.4, J7.6, J7.11, J7.14, J7.19, J7.22, J7.27, J7.30, J7.37, J7.38, J7.40, J8.1, J9.4, J9.7, J9.12, J9.15, J10.5, J10.8, J11.3, J11.4, JP7.1, JP12.1, U1.33, U1.75, U2.1, U2.18, U3.10, U4.1, U4.18, U5.10, U6.7, U7.1, U7.18, U8.10, U9.1, U9.18
unnamed: D1.2, R1.2
unnamed: R14.2, TP97.1, U6.3
unnamed: R15.2, TP98.1, U6.6
