baldengineer/Mega-IIe/kicad files/gd IWM proto pcb/gd IWM proto pcb.kicad_pcb

## KiCad design kicad files/gd IWM proto pcb/gd IWM proto pcb.kicad_pcb (2021-08-27)

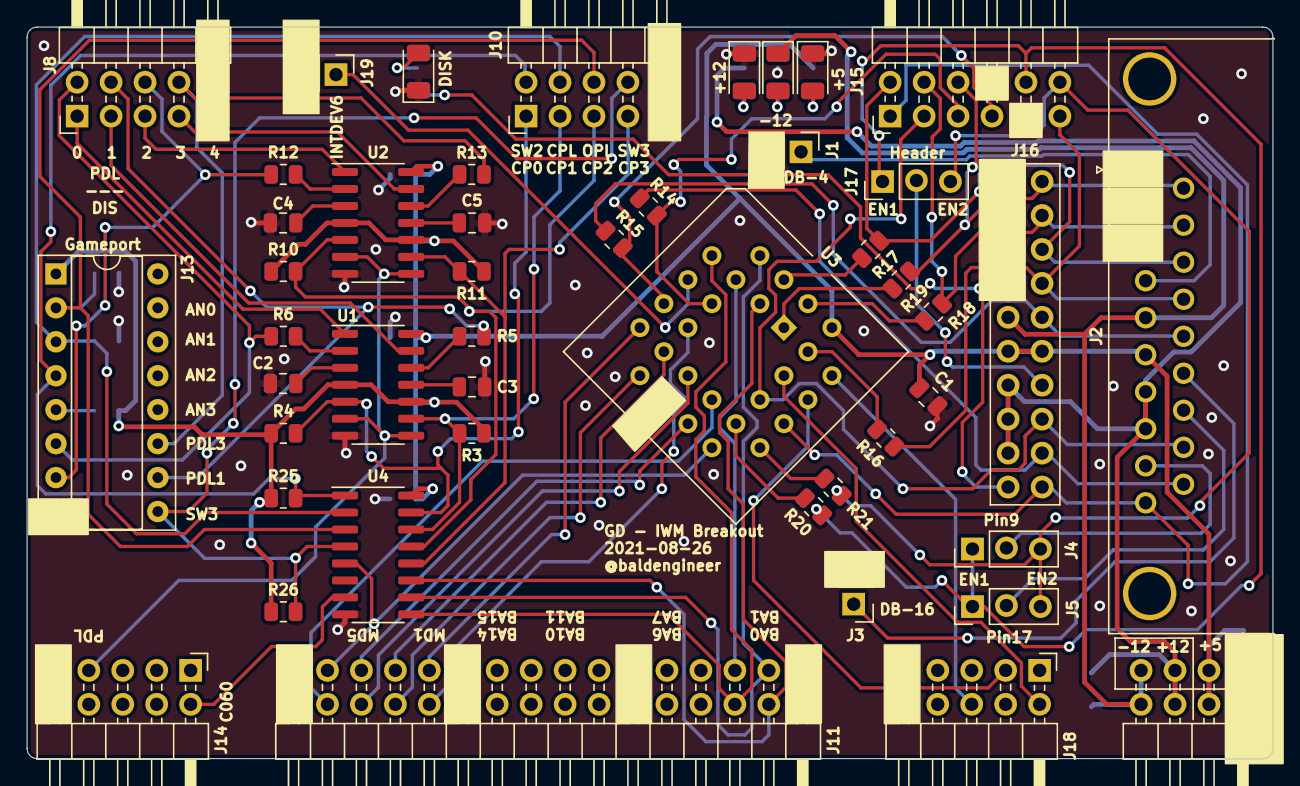
[picture p91: board gd IWM proto pcb.kicad_pcb from above]

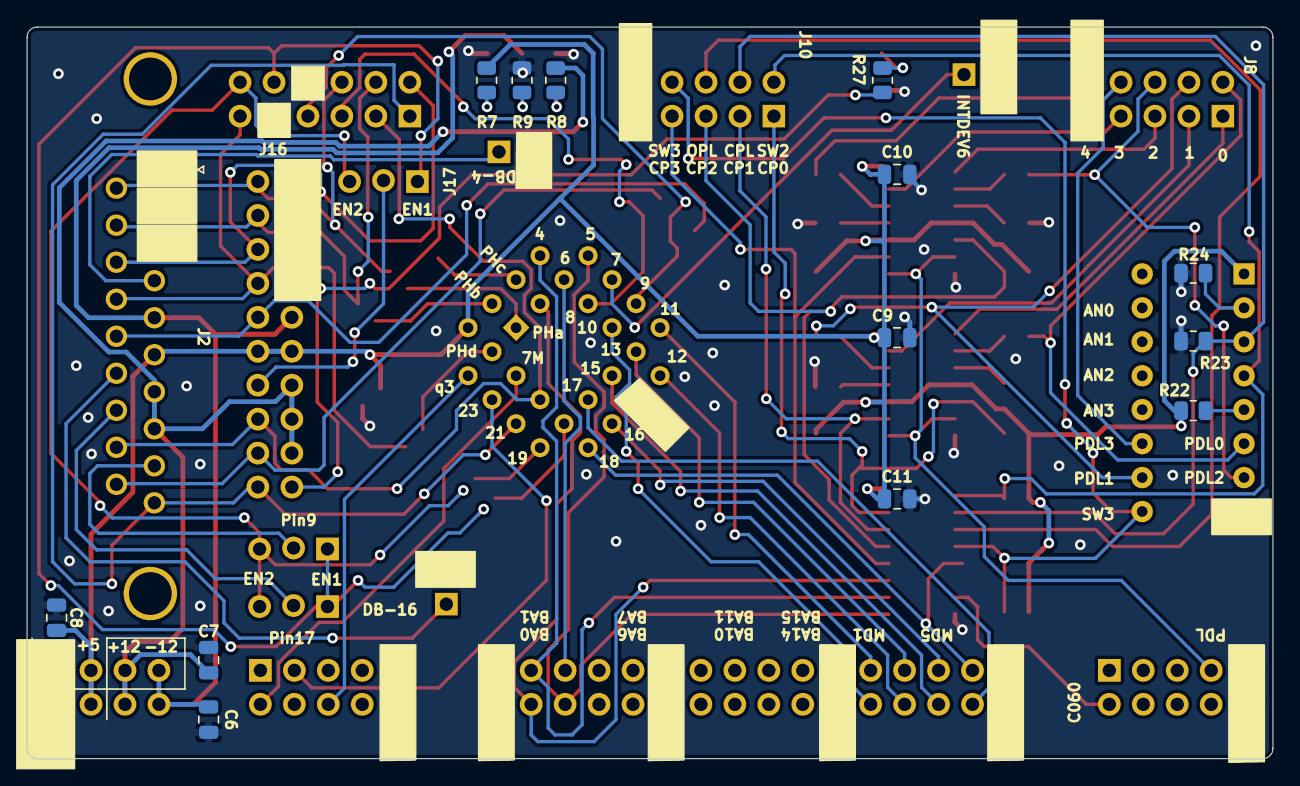
[picture p92: board gd IWM proto pcb.kicad_pcb from below]

Board: 2 copper layers, 93.2 x 54.7 mm, 60 parts (13 on the bottom side), 75 nets.

Parts:
C1, C6, C7, C8: 10u; C_0805_2012Metric
C2, C3, C4, C5: .1u; C_0805_2012Metric
C9, C10, C11: 1u; C_0805_2012Metric
D2: -5v; LED_1206_3216Metric
D3: +5v; LED_1206_3216Metric
D4: +12v; LED_1206_3216Metric
D5: DSK; LED_1206_3216Metric
J1: DB19_4; PinHeader_1x02_P2.54mm_Vertical-LOCK
J2: DSUB19; DSUB-19_Apple_II_Floppy
J3: DB19_16; PinHeader_1x02_P2.54mm_Vertical-LOCK
J4, J5, J17: EN; PinHeader_1x03_P2.54mm_Vertical-LOCK
J6: PWR; PinHeader_2x04_P2.54mm_Horizontal
J8: 555_LA; PinHeader_2x05_P2.54mm_Horizontal
J10: CPx_LA; PinHeader_2x05_P2.54mm_Horizontal
J11: Addr_Main_Data; PinHeader_2x16_P2.54mm_Horizontal
J13: Game Port; DIP-16_W7.62mm_Socket
J14: CTRL2; PinHeader_2x05_P2.54mm_Horizontal
J15: IWM-LA; PinHeader_2x06_P2.54mm_Horizontal
J16: FDC Hdr; PinHeader_2x10_P2.54mm_Vertical
J18: CTRL1; PinHeader_2x05_P2.54mm_Horizontal
J19: Slot_Maker; PinHeader_1x02_P2.54mm_Vertical-LOCK
R3, R4, R10, R11: 1K; R_0805_2012Metric
R5, R6, R12, R13: 100; R_0805_2012Metric
R7, R8, R9: 1k; R_0805_2012Metric
R14, R15, R16, R17, R18, R19, R20, R21: 22; R_0805_2012Metric
R22, R23, R24, R27: 4k7; R_0805_2012Metric
R25, R26: 200k; R_0805_2012Metric
U1, U2: NE556; SO-14_3.9x8.65mm_P1.27mm
U3: IWM; PLCC-28_THT-Socket
U4: HCT251; SOIC-16_3.9x9.9mm_P1.27mm

Connections:
+5V: C1.1, C8.1, C9.1, C10.1, C11.1, J2.6, J6.3, J6.4, J13.1, J16.11, J16.12, R3.1, R4.1, R7.1, R10.1, R11.1, R22.1, R25.1, R26.1, U1.4, U1.10, U1.14, U2.4, U2.10, U2.14, U3.26, U4.16
+12V: C7.1, J2.7, J2.8, J6.5, J6.6, J16.13, J16.15, J16.17, R8.1
-12V: C6.1, D2.1, J2.5, J6.7, J6.8, J16.9
/7M: J18.2, U3.24
/BA0: J11.4, U3.3, U4.11
/BA1: J11.3, U3.4, U4.10
/BA2: J11.6, U3.5, U4.9
/BA3: J11.5, U3.6
/C060-67: J14.2, U4.7
/CP0: J10.1, R4.2, U1.5, U4.15
/CP1: J10.3, R3.2, U1.9, U4.14
/CP2: J10.5, R10.2, U2.5, U4.13
/CP3: J10.7, R11.2, U2.9, U4.12
/DB19-4: J1.1, J2.4
/DB19-16: J2.16, J3.1
/DIS0: J8.1, U1.1
/DIS1: J8.3, U1.13
/DIS2: J8.5, U2.1
/DIS3: J8.7, U2.13
/DiskAct: J16.19, R27.1
/EN1: R20.2, U3.20
/EN2: R21.2, U3.19
/INTDEV6: J19.1, U3.7
/MD0: J11.24, U3.10
/MD1: J11.23, U3.11
/MD2: J11.26, U3.12
/MD3: J11.25, U3.13
/MD4: J11.28, U3.15
/MD5: J11.27, U3.16
/MD6: J11.30, U3.17
/MD7: J11.29, U3.18, U4.5
/PDL0: J8.2, J13.6, R6.1
/PDL1: J8.4, J13.10, R5.1
/PDL2: J8.6, J13.7, R12.1
/PDL3: J8.8, J13.11, R13.1
/PDLTRIG: J14.7, U1.6, U1.8, U2.6, U2.8
/PHa: R19.2, U3.1
/PHb: R18.2, U3.28
/PHc: R17.2, U3.2
/PHd: R16.2, U3.27
/Q3: J18.6, U3.25
/RDATA: J2.18, J15.3, J16.16, U3.22
/RESET: J18.3, U3.23
/SENSE: J2.10, J15.1, J16.20, U3.21
/STB: J13.5, R22.2
/SW0_OAPL: J10.6, J13.2, R24.1, U4.3
/SW1_CAPL: J10.4, J13.3, R23.1, U4.2
/SW2: J10.2, J13.4, R25.2, U4.1
/SW3: J10.8, J13.9, R26.2, U4.4
/WDATA: J15.5, R14.2, U3.8
/WREQ: J15.7, R15.2, U3.9
/bEN1: J4.1, J5.1, J15.10, J17.1, R20.1
/bEN2: J4.3, J5.3, J15.12, J17.3, R21.1
/bWDATA: J2.19, J16.18, R14.1
/bWREQ: J2.15, J16.10, R15.1
/seek0: J2.11, J15.6, J16.2, R19.1
/seek1: J2.12, J15.4, J16.4, R18.1
/seek2: J2.13, J15.2, J16.6, R17.1
/seek3: J2.14, J15.11, J16.8, R16.1
GND: C1.2, C2.2, C3.2, C4.2, C5.2, C6.2, C7.2, C8.2, C9.2, C10.2, C11.2, D3.1, D4.1, D5.1, J1.2, J2.1, J2.2, J2.3, J3.2, J6.1, J6.2, J8.9, J8.10, J10.9, J10.10, J11.1, J11.2, J11.11, J11.12, J11.21, J11.22, J11.31, J11.32, J13.8, J14.9, J14.10, J15.8, J15.9, J16.1, J16.3, J16.5, J16.7, J18.9, J18.10, J19.2, R9.1, R23.2, R24.2, U1.7, U2.7, U3.14, U4.8
unnamed: C2.1, U1.3
unnamed: C3.1, U1.11
unnamed: C4.1, U2.3
unnamed: C5.1, U2.11
unnamed: D2.2, R9.2
unnamed: D3.2, R7.2
unnamed: D4.2, R8.2
unnamed: D5.2, R27.2
unnamed: J2.9, J4.2
unnamed: J2.17, J5.2
unnamed: J16.14, J17.2
unnamed: R5.2, U1.12
unnamed: R6.2, U1.2
unnamed: R12.2, U2.2
unnamed: R13.2, U2.12
