baldengineer/Mega-IIe/kicad files/gd audio proto pcb/gd audio proto pcb-rev1 bad footprint.kicad_pcb

## KiCad design kicad files/gd audio proto pcb/gd audio proto pcb-rev1 bad footprint.kicad_pcb (2022-01-31)

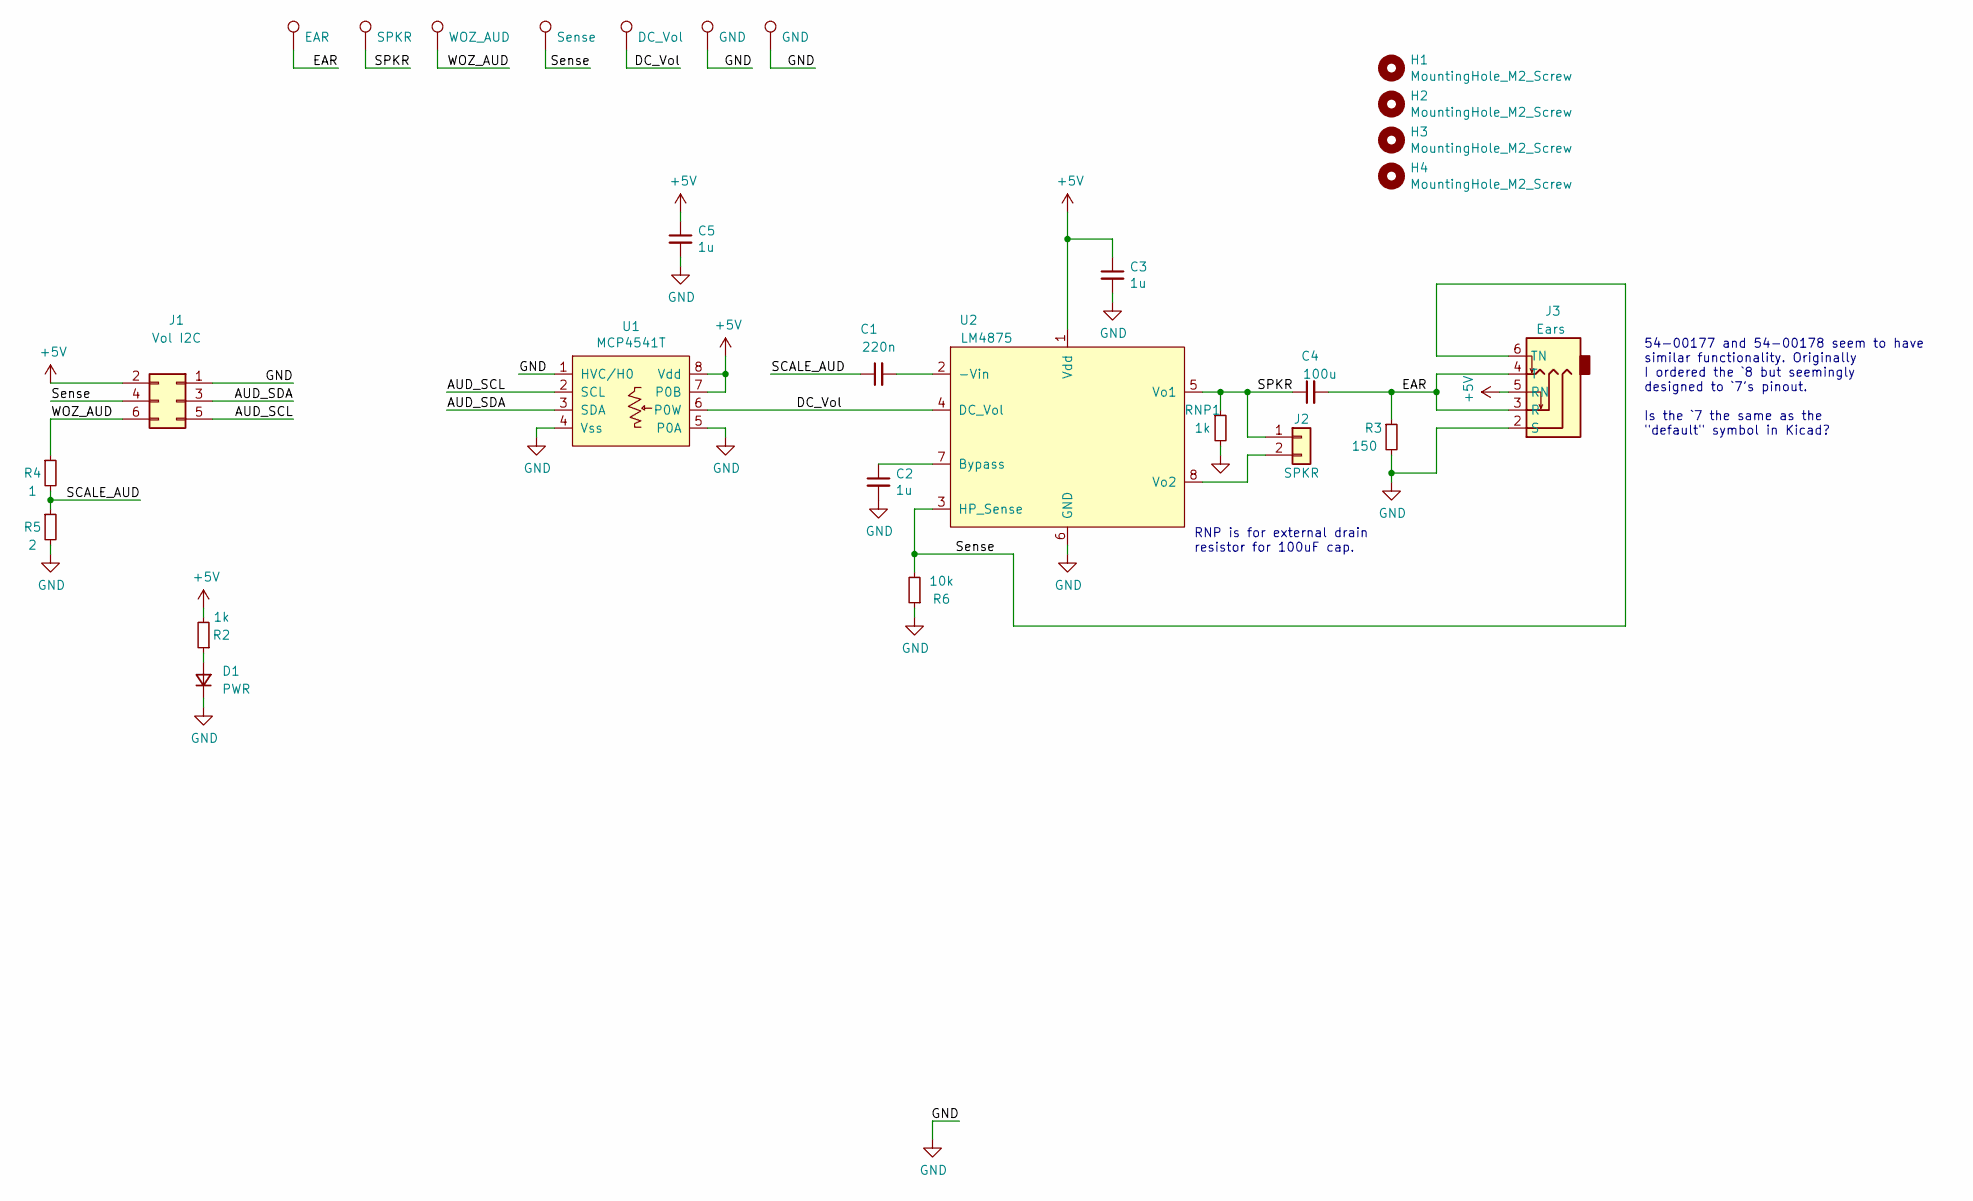
[picture p93: schematic gd audio proto pcb.kicad_sch]

Parts:
C1: 220n; R_1206_3216Metric
C2, C3, C5: 1u; R_0805_2012Metric
C4: 100u; CP_EIA-3216-18_Kemet-A; MPN T520A107M006ATE035
D1: PWR; LED_1206_3216Metric
H1, H2, H3, H4: MountingHole_M2_Screw; MountingHole_2.2mm_M2
J1: Vol I2C; PinHeader_2x03_P2.54mm_Vertical
J2: SPKR; PinHeader_1x02_P2.54mm_Vertical
J3: Ears; Jack_3.5mm_PJ311_Horizontal; MPN 54-00178
R2: 1k; R_0805_2012Metric
R3: 150; R_0805_2012Metric
R4: 1; R_0805_2012Metric
R5: 2; R_0805_2012Metric
R6: 10k; R_0805_2012Metric
RNP1: 1k; R_0805_2012Metric
TP1: EAR; Harwin-S1751-46-Test-Point
TP2: SPKR; Harwin-S1751-46-Test-Point
TP3: WOZ_AUD; Harwin-S1751-46-Test-Point
TP4: Sense; Harwin-S1751-46-Test-Point
TP5: DC_Vol; Harwin-S1751-46-Test-Point
TP6, TP7: GND; Harwin-S1751-46-Test-Point
U1: MCP4541T; MSOP-8_3x3mm_P0.65mm
U2: LM4875; SOIC-8_3.9x4.9mm_P1.27mm

Connections:
+5V: C3.1, C5.1, J1.2, J3.5 (RN), R2.2, U1.7 (P0B), U1.8 (Vdd), U2.1 (Vdd)
/AUD_SCL: J1.5, U1.2 (SCL)
/AUD_SDA: J1.3, U1.3 (SDA)
/DC_Vol: TP5.1, U1.6 (P0W), U2.4 (DC_Vol)
/EAR: C4.2, J3.3 (R), J3.4 (T), R3.1, TP1.1
/SCALE_AUD: C1.1, R4.2, R5.1
/SPKR: C4.1, J2.1, RNP1.1, TP2.1, U2.5 (Vo1)
/Sense: J1.4, J3.6 (TN), R6.2, TP4.1, U2.3 (HP_Sense)
/WOZ_AUD: J1.6, R4.1, TP3.1
GND: C2.2, C3.2, C5.2, D1.1 (K), J1.1, J3.2 (S), R3.2, R5.2, R6.1, RNP1.2, TP6.1, TP7.1, U1.1 (HVC/H0), U1.4 (Vss), U1.5 (P0A), U2.6 (GND)
unnamed: C1.2, U2.2 (-Vin)
unnamed: C2.1, U2.7 (Bypass)
unnamed: D1.2 (A), R2.1
unnamed: J2.2, U2.8 (Vo2)

Notes on the sheet:
RNP is for external drain resistor for 100uF cap.
54-00177 and 54-00178 seem to have similar functionality. Originally I ordered the `8 but seemingly designed to `7's pinout. Is the `7 the same as the "default" symbol in Kicad?

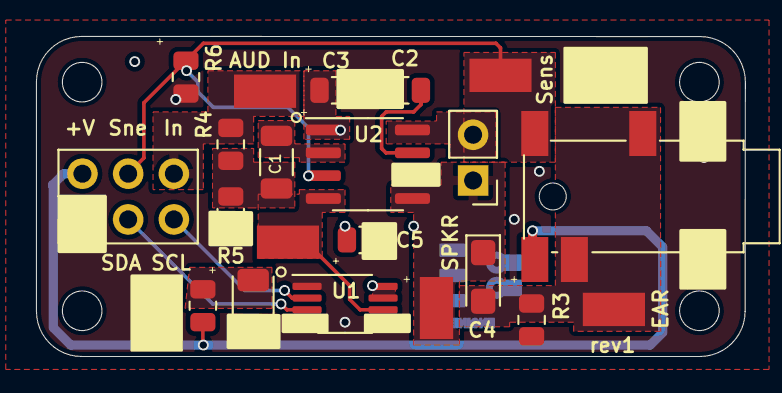
[picture p94: board gd audio proto pcb-rev1 bad footprint.kicad_pcb from above]

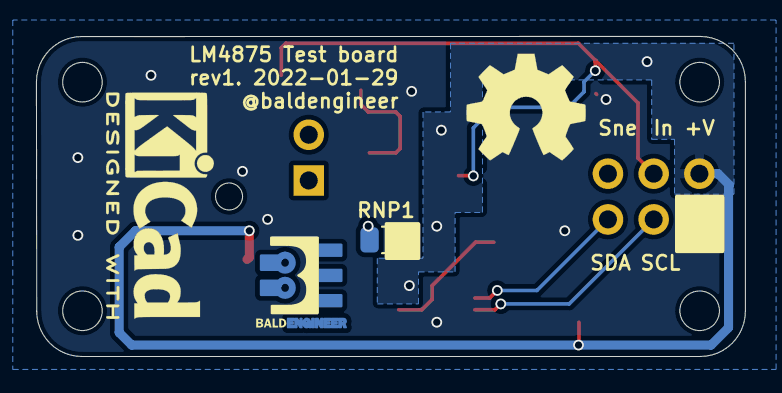
[picture p95: board gd audio proto pcb-rev1 bad footprint.kicad_pcb from below]

Board: 2 copper layers, 39.4 x 17.8 mm, 29 parts (2 on the bottom side), 14 nets.

Other parts of the board:
svg2mod: G***; BE5v2
