baldengineer/Mega-IIe/firmware/IIe-keyboard_emulator/src/iie_hid_app.c

/*
 * The MIT License (MIT)
 *
 * Copyright (c) 2021, Ha Thach (tinyusb.org)
 * Copyright (c) 2022 James Lewis
 *
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
 */


//#include "hid_host.h"

//#define DEBUG_IIE_HID

#include "bsp/board.h"
#include "tusb.h"
#include <iie_hid_app.h>
#include <keyboard_mapping.h>
#include "constants.h"
#include "enums.h"

#define MAX_REPORT 4

extern int audio_volume;
extern bool audio_mute;
extern bool audio_variable_debug;
extern struct Macro_list function_key_macros;
bool control_key = false;


void hid_app_task(void) {
    // nothing to do
}

//--------------------------------------------------------------------+
// TinyUSB Callbacks
//--------------------------------------------------------------------+

// Invoked when device with hid interface is mounted
// Report descriptor is also available for use. tuh_hid_parse_report_descriptor()
// can be used to parse common/simple enough descriptor.
// Note: if report descriptor length > CFG_TUH_ENUMERATION_BUFSIZE, it will be skipped
// therefore report_desc = NULL, desc_len = 0


void tuh_hid_mount_cb(uint8_t dev_addr, uint8_t instance, uint8_t const* desc_report, uint16_t desc_len) {
    printf("HID device address = %d, instance = %d is mounted\r\n", dev_addr, instance);

    // Interface protocol (hid_interface_protocol_enum_t)
    const char* protocol_str[] = {"None", "Keyboard", "Mouse"};
    uint8_t const itf_protocol = tuh_hid_interface_protocol(dev_addr, instance);

    printf("HID Interface Protocol = %s\r\n", protocol_str[itf_protocol]);

    // By default host stack will use activate boot protocol on supported interface.
    // Therefore for this simple example, we only need to parse generic report descriptor (with built-in parser)
    if (itf_protocol == HID_ITF_PROTOCOL_NONE) {
        hid_info[instance].report_count = tuh_hid_parse_report_descriptor(hid_info[instance].report_info, MAX_REPORT, desc_report, desc_len);
        printf("HID has %u reports \r\n", hid_info[instance].report_count);
    }

    // request to receive report
    // tuh_hid_report_received_cb() will be invoked when report is available
    if (!tuh_hid_receive_report(dev_addr, instance)) {
        printf("Error: cannot request to receive report\r\n");
    }
    if (dev_addr == 0x1 && instance == 0x1){
        // wtf_bbq_led(0x2);
        kbd_connected = true;
        printf("\nForcing Caps Lock to High\n");
        shift_lock_state = true;
        imma_led(0x2); // because we don't have a funciton to do it
    }


}

// Invoked when device with hid interface is un-mounted
void tuh_hid_umount_cb(uint8_t dev_addr, uint8_t instance) {
    printf("HID device address = %d, instance = %d is unmounted\r\n", dev_addr, instance);
}

// Invoked when received report from device via interrupt endpoint
void tuh_hid_report_received_cb(uint8_t dev_addr, uint8_t instance, uint8_t const* report, uint16_t len) {
    uint8_t const itf_protocol = tuh_hid_interface_protocol(dev_addr, instance);

    switch (itf_protocol) {
        case HID_ITF_PROTOCOL_KEYBOARD:
            TU_LOG2("HID receive boot keyboard report\r\n");
            process_kbd_report((hid_keyboard_report_t const*)report);
            break;

        default:
            // Generic report requires matching ReportID and contents with previous parsed report info
            process_generic_report(dev_addr, instance, report, len);
            break;
    }

    // continue to request to receive report
    if (!tuh_hid_receive_report(dev_addr, instance)) {
        printf("Error: cannot request to receive report\r\n");
    }
}

//--------------------------------------------------------------------+
// Keyboard
//--------------------------------------------------------------------+
/*
  explains keyboard packets (verbosely): https://wiki.osdev.org/USB_Human_Interface_Devices
  explains setup packet: https://www.beyondlogic.org/usbnutshell/usb6.shtml
*/
void imma_led(uint8_t state) {
    static uint32_t call_counter = 0;
    uint8_t dev_addr    = 0x01;
    uint8_t instance    = 0x00;
    uint8_t report_id   = 0x00;
    uint8_t report_type = 0x02;

    D(printf("%d: imma led: %d\n", call_counter++,kbd_led_state[0]);)
    if (state == 0x2)
        kbd_led_state[0] = kbd_led_state[0] | 0x02;
    if (state == 0x0)
        kbd_led_state[0] = kbd_led_state[0] & 0xFD;

    tuh_hid_set_report(dev_addr, instance, report_id, report_type, kbd_led_state, 1);
}

inline static uint8_t get_ascii(uint8_t keyboard_code, uint8_t mod_keys) {
    bool is_shift = mod_keys & (KEYBOARD_MODIFIER_LEFTSHIFT | KEYBOARD_MODIFIER_RIGHTSHIFT);
    //bool const is_ctrl = mod_keys & (KEYBOARD_MODIFIER_LEFTCTRL | KEYBOARD_MODIFIER_RIGHTCTRL);
    bool is_ctrl = control_key;

    // this mirrors how IIe works (but not IIgs, I think)
    if (shift_lock_state && (keyboard_code >= 4) && (keyboard_code <= 29))  //a=4, z=29
        is_shift = true;
    
    uint8_t ch = 0x0;
    if (is_shift && is_ctrl)
        ch = both_kbd_map[keyboard_code];
    else if (is_shift)
        ch = shift_kbd_map[keyboard_code];
    else if (is_ctrl) 
        ch = ctrl_kbd_map[keyboard_code];
    else
        ch = normal_kbd_map[keyboard_code];

    printf("[%d], ascii[%d]\n", keyboard_code, ch);

    return ch;
}

static void handle_special_sequences(hid_keyboard_report_t const* report, uint8_t modifiers) {
        // looking for special key sequences

    if (modifiers > 0) {
        // menu key is 0x10
        printf("Modifier: [%x]\n", modifiers);

        if ((modifiers & 0x01))
            caps_lock_toggle();

        // left-windows key (open-apple)
        if ((modifiers & 0x04)) //0x08 is normal windows key
            OAPL_state = true;

        // right-windows key (closed-apple)
        if ((modifiers & 0x40)) //0x80 is normal windows key
            CAPL_state = true;

        // ctrl-alt-delete (same as IIe ctrl-reset)
        // if ((modifiers == 5))
        //     for (uint8_t i = 0; i < 6; i++) {
        //         if (report->keycode[i]==76)
        //             do_a_reset = true;
        //     }
        if ((modifiers & 0x04)) {
            uint8_t key_count = 0;
            for (uint8_t i = 0; i < 6; i++) {
                if (report->keycode[i]==76)
                    key_count++;
                if (report->keycode[i]==57)
                    key_count++;
            }
            if (key_count == 2)
                do_a_reset = true;
        }
    }
}

static void find_new_keys(hid_keyboard_report_t const* report,hid_keyboard_report_t const* prev_report, uint8_t report_count, uint8_t modifiers ) {
    D(printf("Getting new keys...\n");)
    for (int i=0; i < report_count; i++) {
        uint8_t curr_keycode = report->keycode[i];
        uint8_t prev_keycode = prev_report->keycode[i];
        char curr_char = get_ascii(curr_char, modifiers);

        if (curr_keycode != prev_keycode) {
            D(printf("Queuing: [%d] %c\n", curr_keycode, curr_char);)
            queue_key(get_ascii(curr_keycode, modifiers));
            last_key_pressed = get_ascii(curr_keycode, modifiers); // last one in report is the "last" key pressed
        } else {
            D(printf("Repeated: %d\n", curr_keycode, curr_char);)
        }
    }
}

static void caps_lock_toggle() {
    D(printf("Caps Lock\n");)
    shift_lock_state = !shift_lock_state;
    if (shift_lock_state)
        imma_led(0x2);
    else
        imma_led(0x0);
    D(printf("Shift Lock: %d\n", shift_lock_state);)
}

static void process_kbd_report(hid_keyboard_report_t const* report) {
    static hid_keyboard_report_t prev_report = {0, 0, {0}};  // previous report to check key released
    static uint8_t prev_report_count = 0;
    static uint8_t prev_modifiers = 0;
  
    modifiers = report->modifier;

    OAPL_state = false;
    CAPL_state = false;
    if (modifiers > 0) {
        handle_special_sequences(report, modifiers);
    }

    // count the current reports
    bool special_function = false;
    control_key = false;
    uint8_t report_count = 0;
    for (uint8_t i = 0; i < 6; i++) {
        if (report->keycode[i] > 0) {
            if (((report->keycode[i] >= 57) && (report->keycode[i] <= 72)))
                special_function = true;
            report_count++;
        }
    }

    if ((report_count > 0)) {
        // print the report
        D(printf("Report: (%lu) ", (unsigned long)time_us_32());)
        for (uint8_t i = 0; i < 6; i++) {
                D(printf("%d [%c],", report->keycode[i], get_ascii(report->keycode[i], modifiers));)
        }
        D(printf("\n");)
    }

    // Condition #0: does this current report contain caps, Fx, restore, 40/80 or Run/stop?
    if (special_function) {
        bool is_shift = modifiers & (KEYBOARD_MODIFIER_LEFTSHIFT | KEYBOARD_MODIFIER_RIGHTSHIFT);
        function_key_macros.shift = is_shift;
        for (uint8_t i = 0; i < report_count; i++) {
            switch (report->keycode[i]) {

                case CTRL_KEY: // ctrl key on mega keyboard (caps on others)
                    control_key = true;
                break;

                case F1:
                    function_key_macros.Print = true;
                break;
                case F2:
                    function_key_macros.Input = true;
                break;
                case F3:
                    function_key_macros.Poke = true;
                break;
                case F4:
                    function_key_macros.Peek = true;
                break;
                case F5:
                    function_key_macros.Call = true;
                break;
                case F6:
                    function_key_macros.PR = true;
                break;
                case F7:
                    function_key_macros.Text = true;
                break;
                case F8:
                    function_key_macros.Home = true;
                break;
                case F9:
                    function_key_macros.n151 = true;
                break;
                case F10:
                    function_key_macros.x3F4 = true;
                break;
                case F11:
                    function_key_macros.p1012 = true;
                break;

                case F12:
                    D(printf("[%d] F12\n",report->keycode[i]);)
                    power_cycle_timer = time_us_32();
                    power_cycle_key_counter++;
                    D(printf("PWR Cycle Count: (%d)\n", power_cycle_key_counter);)
                break;

                case VOL_DOWN: // now volume down, was restore
                    if (is_shift)
                        audio_volume++;
                    else     
                        audio_volume += 10;
                    if (audio_volume > MCP4541_MAX_STEPS)
                        audio_volume = MCP4541_MAX_STEPS;
                    printf("Volume Down...[%d]\n", audio_volume);
                break;

                case VOL_MUTE:
                    if (is_shift) {
                        audio_variable_debug = true;
                    } else  {
                        audio_mute = !audio_mute;
                    }
                break;

                case VOL_UP: // now volume up, was 40/80
                    if (is_shift)
                        audio_volume--;
                    else
                        audio_volume -= 10;
                    if (audio_volume <= MCP4541_MIN_STEPS)
                        audio_volume = MCP4541_MIN_STEPS;
                    printf("Volume Up...[%d]\n", audio_volume);
                break;

                default:
                    printf("Got Special Function: [%d]\n",report->keycode[i]);
            }
        }
    }

    // Condition #1: was previous report AND this report empty? ignore it
    if ((prev_report_count==0) && (report_count==0)) {
        D(printf("Ignorning report\n\n\n");)
        nkey = NKEY_IDLE;
        prev_report_count = report_count;
        prev_report = *report;       
        return;
    }

    //  Condition #2: did previous report have keys but this one is empty? then release everything
    if ((prev_report_count>0) && (report_count==0)) {
        D(printf("All Keys Released\n\n");)
        raise_key();
        nkey = NKEY_IDLE;
        prev_report_count = report_count;
        prev_report = *report;         
    }

    // Condition #3: was previous report empty? AND this report is not if so, queue up each key (new event)
    if ((prev_report_count==0) && (report_count>0)) {
        nkey = NKEY_NEW;
        for (uint8_t i = 0; i <= report_count; i++) {
            if (report->keycode[i] > 0) {
                uint8_t ascii = get_ascii(report->keycode[i], modifiers);
                queue_key(ascii);
                last_key_pressed = ascii; // last one in report is the "last" key pressed
                D(printf("W[%d]\n",ascii));
            }
        }
    }

    // Condition #4: did previous report and this report have keys?
    if ((prev_report_count > 0) && (report_count>0)) {
        // a new key was added to the queue
        nkey = NKEY_NEW;
        D(printf("BTB Reports with Keys\n");)
        if ((report_count >= prev_report_count)) {
            // queue the new keys
            find_new_keys(report, &prev_report, report_count, modifiers);
        }
    }
    prev_report_count = report_count;
    prev_report = *report;
}

//--------------------------------------------------------------------+
// Generic Report
//--------------------------------------------------------------------+
static void process_generic_report(uint8_t dev_addr, uint8_t instance, uint8_t const* report, uint16_t len) {
    (void)dev_addr;

    uint8_t const rpt_count = hid_info[instance].report_count;
    tuh_hid_report_info_t* rpt_info_arr = hid_info[instance].report_info;
    tuh_hid_report_info_t* rpt_info = NULL;

    if (rpt_count == 1 && rpt_info_arr[0].report_id == 0) {
        // Simple report without report ID as 1st byte
        rpt_info = &rpt_info_arr[0];
    } else {
        // Composite report, 1st byte is report ID, data starts from 2nd byte
        uint8_t const rpt_id = report[0];

        // Find report id in the arrray
        for (uint8_t i = 0; i < rpt_count; i++) {
            if (rpt_id == rpt_info_arr[i].report_id) {
                rpt_info = &rpt_info_arr[i];
                break;
            }
        }

        report++;
        len--;
    }

    if (!rpt_info) {
        printf("Couldn't find the report info for this report !\r\n");
        return;
    }

    // For complete list of Usage Page & Usage checkout src/class/hid/hid.h. For examples:
    // - Keyboard                     : Desktop, Keyboard
    // - Mouse                        : Desktop, Mouse
    // - Gamepad                      : Desktop, Gamepad
    // - Consumer Control (Media Key) : Consumer, Consumer Control
    // - System Control (Power key)   : Desktop, System Control
    // - Generic (vendor)             : 0xFFxx, xx
    if (rpt_info->usage_page == HID_USAGE_PAGE_DESKTOP) {
        switch (rpt_info->usage) {
            case HID_USAGE_DESKTOP_KEYBOARD:
                TU_LOG1("HID receive keyboard report\r\n");
                // Assume keyboard follow boot report layout
                process_kbd_report((hid_keyboard_report_t const*)report);
                break;

            default:
                break;
        }
    }
}
