baldengineer/Mega-IIe/firmware/IIe-keyboard_emulator/src/power_sequence.c

#include <stdio.h>
#include "hardware/clocks.h"
#include "hardware/pio.h"
#include "hardware/timer.h"
#include "hardware/watchdog.h"
#include "pico/stdlib.h"

#include "constants.h"

extern void out_init(uint8_t pin, bool state);

//void handle_mega_power_button();
void handle_power_sequence(uint8_t state);
void setup_power_sequence();

extern bool mega_power_state;
extern int audio_volume;

void setup_power_sequence() {
    // Init Outputs and turn it all off
    gpio_init_mask(PWR_SEQ_MASK);
    gpio_put_masked(PWR_SEQ_MASK, 0x0);   // does this set the value for output before enabling it?
    gpio_set_dir_out_masked(PWR_SEQ_MASK);
    gpio_put_masked(PWR_SEQ_MASK, 0x0);

    // // Get Mega Power Button Ready Rev3 doesn't have a mega button :(
    // gpio_init(MEGA_POWER);
    // gpio_set_input_enabled(MEGA_POWER, true);
    // gpio_pull_up(MEGA_POWER);
}

// inline void handle_mega_power_button() {
//     static bool prev_mega_power = NOT_PRESSED;

//     bool curr_mega_power = gpio_get(MEGA_POWER);

//     if (curr_mega_power != prev_mega_power) {
//         if (curr_mega_power == PRESSED) {
//             mega_power_state = !mega_power_state;
//             handle_power_sequence(mega_power_state);
//         }
//         prev_mega_power = curr_mega_power;
//     }
// }

void handle_power_sequence(uint8_t state) {
    // state 0: turn off everything
    // state 1: turn on everything
    // state 2: power cycle
    switch(state) {
        case PWR_OFF:
            printf("\nTurning off supplies...\n");
            out_init(RESET_CTL, 0x1);
            gpio_put_masked(PWR_SEQ_MASK, 0x0);
        break;

        case PWR_ON:
            printf("\nTurning on Supplies...\n");
            out_init(RESET_CTL, 0x1);
            gpio_put_masked(PWR_SEQ_MASK, PWR_SEQ_MASK); // mask has the bits we want
            busy_wait_ms(50);
            audio_volume = read_mcp4541_eeprom();
            if (audio_volume >= 0)
                printf("Audio set to [%d] step(s)\n", audio_volume);
            else
                printf("ERROR: Audio Pot did not respond!\n");
            out_init(RESET_CTL, 0x0);
        break;

        case 2:
            printf("\nCycling Power\n");
            printf("Off...");
            out_init(RESET_CTL, 0x1);
            gpio_put_masked(PWR_SEQ_MASK, 0x0);
            busy_wait_ms(250);
            printf("---");
            busy_wait_ms(250);
            printf("On...\n");
            gpio_put_masked(PWR_SEQ_MASK, PWR_SEQ_MASK);
            busy_wait_ms(50);
            out_init(RESET_CTL, 0x0);
        break;
    }
}
