baldengineer/Mega-IIe/firmware/mega2_picovga/vga_mega2/src/include.h

// ****************************************************************************
//                                 
//                              Common definitions
//
// ****************************************************************************

// ----------------------------------------------------------------------------
//                                   Includes
// ----------------------------------------------------------------------------


#include "../../global.h"	// global common definitions
#include "../vga.pio.h"		// VGA PIO compilation
#include "../TEST_CAP.pio.h" //Test Capture
