baldengineer/Mega-IIe/firmware/IIe-keyboard_emulator/src/keyboard_mapping.h

uint8_t normal_kbd_map[] = {
0x0,0x0,0x0,0x0,0x61,0x62,0x63,0x64,
0x65,0x66,0x67,0x68,0x69,0x6A,0x6B,0x6C,
0x6D,0x6E,0x6F,0x70,0x71,0x72,0x73,0x74,
0x75,0x76,0x77,0x78,0x79,0x7A,0x31,0x32,
0x33,0x34,0x35,0x36,0x37,0x38,0x39,0x30,
0x0D,0x1B,0x7F,0x09,0x20,0x2d,0x3d,0x5b,
0x5d,0x5c,0x7e,0x3b,0x27,0x60,0x2c,0x2e,
0x2f,0x0,0x0,0x0,0x0,0x0,0x0,0x0,
0x0,0x0,0x0,0x0,0x0,0x0,0x0,0x0,
0x0,0x0,0x0,0x0,0x0,0x0,0x0,0x15,
0x08,0x0A,0x0B,0x0,0x0,0x0,0x0,0x0,
0x0,0x0,0x0,0x0,0x0,0x0,0x0,0x0,
0x0,0x0,0x0,0x0,0x0,0x0,0x0,0x0,
0x0,0x0,};

uint8_t ctrl_kbd_map[] = {
0x0,0x0,0x0,0x0,0x01,0x02,0x03,0x04,
0x05,0x06,0x07,0x08,0x09,0x0A,0x0B,0x0C,
0x0D,0x0E,0x0F,0x10,0x11,0x12,0x13,0x14,
0x15,0x16,0x17,0x18,0x19,0x1A,0x31,0x00,
0x33,0x34,0x35,0x1E,0x37,0x38,0x39,0x30,
0x0D,0x1B,0x7F,0x09,0x20,0x1f,0x3d,0x1b,
0x1d,0x1c,0x7e,0x3b,0x27,0x60,0x2c,0x2e,
0x2f,0x0,0x0,0x0,0x0,0x0,0x0,0x0,
0x0,0x0,0x0,0x0,0x0,0x0,0x0,0x0,
0x0,0x0,0x0,0x0,0x0,0x0,0x0,0x15,
0x08,0x0A,0x0B,0x0,0x0,0x0,0x0,0x0,
0x0,0x0,0x0,0x0,0x0,0x0,0x0,0x0,
0x0,0x0,0x0,0x0,0x0,0x0,0x0,0x0,
0x0,0x0,};

uint8_t shift_kbd_map[] = {
0x0,0x0,0x0,0x0,0x41,0x42,0x43,0x44,
0x45,0x46,0x47,0x48,0x49,0x4A,0x4B,0x4c,
0x4d,0x4e,0x4f,0x50,0x51,0x52,0x53,0x54,
0x55,0x56,0x57,0x58,0x59,0x5A,0x21,0x40,
0x23,0x24,0x25,0x5E,0x26,0x2A,0x28,0x29,
0x0D,0x1B,0x7F,0x09,0x20,0x5f,0x2b,0x7b,
0x7d,0x7c,0x60,0x3a,0x22,0x7E,0x3c,0x3e,
0x3f,0x0,0x0,0x0,0x0,0x0,0x0,0x0,
0x0,0x0,0x0,0x0,0x0,0x0,0x0,0x0,
0x0,0x0,0x0,0x0,0x0,0x0,0x0,0x15,
0x08,0x0A,0x0B,0x0,0x0,0x0,0x0,0x0,
0x0,0x0,0x0,0x0,0x0,0x0,0x0,0x0,
0x0,0x0,0x0,0x0,0x0,0x0,0x0,0x0,
0x0,0x0,};

uint8_t both_kbd_map[] = {
0x0,0x0,0x0,0x0,0x01,0x02,0x03,0x04,
0x05,0x06,0x07,0x08,0x09,0x0A,0x0B,0x0C,
0x0D,0x0E,0x0F,0x10,0x11,0x12,0x13,0x14,
0x15,0x16,0x17,0x18,0x19,0x1A,0x21,0x00,
0x23,0x24,0x25,0x1e,0x26,0x2a,0x28,0x29,
0x0D,0x1B,0x7F,0x09,0x20,0x1f,0x2b,0x1b,
0x1d,0x1c,0x60,0x3a,0x22,0x7e,0x3c,0x3e,
0x3f,0x0,0x0,0x0,0x0,0x0,0x0,0x0,
0x0,0x0,0x0,0x0,0x0,0x0,0x0,0x0,
0x0,0x0,0x0,0x0,0x0,0x0,0x0,0x15,
0x08,0x0A,0x0B,0x0,0x0,0x0,0x0,0x0,
0x0,0x0,0x0,0x0,0x0,0x0,0x0,0x0,
0x0,0x0,0x0,0x0,0x0,0x0,0x0,0x0,
0x0,0x0,};

//[Finished in 120ms]
